nickraymond/nereus_Pi_shield_ADIN2111/docs/design-review/qe/S7.md

# QE reviews — S7 (PR #29 S7.a)

*Reports from the standing S7 Quality Engineer session (started 2026-10-07 from a task chip, Opus 5.5 high, read-only),
sent straight to the design session and saved by the design agent. Newest round first. Design-agent responses follow
each round.*

---

## PR #29 (S7.a) — Round 3 — 2026-10-07 — APPROVED

**Reviewed:** cce774f (b8083da + cce774f vs 2339368; base b365929), from a `git archive` copy; no fetch.

| Claim | Result | Evidence (summary) |
|---|---|---|
| R2-N1 Bus row names only the T1/T2 data legs and D4/D5 TVS legs | PASS | matches pcbnew |
| R2-N2 | PASS (moot) | the notch was then removed |
| Nick: plain 46 × 65 rectangle, r 3, no notch; §11 notch bullets gone | PASS | no notch coordinates left anywhere; also clears round 1's H2 keep-out point |
| Nick: QE agent file carries the D31 exception | PASS | wording matches CLAUDE.md, SPEC c1, TRACKER 8/9; round-1 N5 closed |
| Round-2 report recorded faithfully; TRACKER, checklist (script parses) | PASS | |
| No schematic / board / reference / Archive / tools change; checks unchanged | PASS | ERC 0 / 494, ercexclude 18/0/0/0, midwire 0, netcheck 51/51 |

| # | Severity | Finding |
|---|---|---|
| R3-N1 | NIT | TRACKER and checklist don't record round 3 |
| R3-N2 | NIT | round-2 response mentions the notch spans that cce774f superseded |

Repo untouched (clean before/after).

### Design-agent response
R3-N1: TRACKER and checklist record round 3. R3-N2: round-2 response annotated.

---

## PR #29 (S7.a) — Round 2 — 2026-10-07 — APPROVED WITH NITS

**Reviewed:** 2339368 (diff vs e735ed6; base b365929), from a `git archive` copy; no fetch this round.

| Claim | Result | Evidence (summary) |
|---|---|---|
| F1 pullback 3.85–4.78 mm in SPEC, BRIEF §4, PR body | PASS | matches the round-1 point-to-segment measurement |
| F2 §6 classes for new routing only; §8.4 / §8.5 consistent | PASS | every mote bus track under 1.0 mm ends at D4/D5 or T1/T2 pins 6/7, so the carve-outs cover them |
| F3 notch transform, shape, edge exemption, §11 | PASS | maps Nick's x 193.78–225.28 to −0.75…30.75; ≈ 2.76 mm from H2 |
| F4 renderer net names | PASS | shield-style names map to bus / pin / pi5v / rail / data / 3v3; switch nets stay signal; mote re-render OK |
| F5 D31 wording, D6 stands | PASS | DESIGN D31, BRIEF §11 |
| N1–N4; N5 left for Nick | PASS / accepted | |
| Round-1 report saved faithfully; TRACKER, checklist (script parses) | PASS | |
| No schematic / board change; checks unchanged | PASS | ERC 0 / 494, ercexclude 18/0/0/0, midwire 0, netcheck 51/51 |

| # | Severity | Finding |
|---|---|---|
| R2-N1 | NIT | §6 mentions "0.2 mm test-point taps" on the bus nets; the mote has none (narrow bus copper ends at T1/T2 pins 6/7 or D4/D5) |
| R2-N2 | NIT | §2's notch span x 5.84…25.66 is where the chamfers start; at the edge it is 4.42–27.08, at full depth 7.58–23.91 |

Repo untouched (clean before/after).

### Design-agent response
R2-N1: the Bus row now names only the data legs to T1/T2 (0.2 mm) and the TVS legs to D4/D5 (0.5 mm). R2-N2: §2 quotes
the edge and full-depth spans (notch later removed by Nick, cce774f). (Round 1's response above mentions "test-point taps"; left as recorded.)

---

## PR #29 (S7.a) — Round 1 — 2026-10-07 — CHANGES REQUESTED

**Reviewed:** e735ed6 vs b365929, from `git archive` copies; BRIEF, KICKOFF, render_layers.py, CLAUDE.md, SPEC, TRACKER,
DESIGN D31, SOFAR_QUESTIONS, DEV_LOG, checklist. Mote board read with pcbnew (never saved); Pi drawing RP-008358-DS-1 and
the Bourns SRF1260 datasheet fetched.

| Claim | Result | Evidence (summary) |
|---|---|---|
| No schematic / board / reference / Archive change; check.sh unchanged | PASS | ERC 0 / 494, ercexclude 18/0/0/0, midwire 0, netcheck 51/51 |
| Pi Zero 2 W holes, header, pin 1 (25.23, 8.37), pins 39/40 y 56.63, orientation | PASS | Drawing: 65 × 30, holes 3.5 in, header centre 3.5 + 29; 90° CW rotation, not a mirror |
| J1 on B.Cu puts pin 2 east of pin 1; courtyard clears H2/H4 | PASS | by 0.07 / 0.13 mm |
| Insert arc, 7 vias at r 3.0, ring pad r 2.2–3.69, body Ø6 × 1.5 | PASS | pcbnew; D24 |
| Planes 4.1–4.8 mm from inserts | **FAIL** | 3.85 mm at MP2/MP4 (F1) |
| Insert placement, pocket, squeeze band, U1 courtyard, Micro-Fit courtyard, J5 vs L1 (0.09 mm), L2, M3 vs inserts | PASS | geometry checked |
| Block ref lists vs schematic | PASS | every ref in exactly one row; TP38 not on the mote (N1) |
| ADIN pair lengths, vias through-only | PASS | 9.47 / 8.01 / 18.25 / 21.30 mm |
| Sofar Q9–Q12 claims | PASS | datasheet windings 1–3, 2–4; nets and fitted state; slots, islands, stackup |
| render_layers.py → six SVGs | PASS (mote) | shield names fail the colour map (F4) |
| Scoped exception wording; SPEC via fact; TRACKER / checklist / DEV_LOG | PASS | plane distance aside (F1) |
| Area-check percentages | not verified | labelled an estimate |

| # | Severity | Finding |
|---|---|---|
| F1 | MINOR | Plane pullback is 3.85 mm (MP2/MP4) to 4.78 mm (MP1/MP3), not 4.1–4.8 (SPEC, BRIEF §4, PR body) |
| F2 | MAJOR | §6 bus ≥ 1.0 mm and VBUS/P_IN ≥ 0.5 mm contradict the copper §5/§8.4 say to copy exactly (0.2 mm bus legs to T1/T2 and taps, 0.5 mm to D4/D5, 0.2 mm sense legs), so §8.4 and §8.5 can't both pass |
| F3 | MINOR | The SD notch's east end is inside H2's r 3.0 keep-out (≈ 2.76 mm on Nick's shape); its x values rest on an unstated mapping, and the brief describes a rectangle where Nick drew a fillet–chamfer–fillet notch |
| F4 | MINOR | render_layers.py matches bare net names; the shield's nets are hierarchical, so its renders lose the bus / P_IN / Pi 5 V / AVDD colours |
| F5 | MINOR | D6 (plain socket, no stacking header) contradicts D31 ("also the target for the real layout") |
| N1 | NIT | TP38 is new (5V_PI), filed under "as on the mote" |
| N2 | NIT | "Mote parts not on the shield" omits U9, D6, D7, R9, R10 |
| N3 | NIT | ADIN pairs are on L1 + L2 on the mote, not "on L2" |
| N4 | NIT | Hole_M3 courtyard / silk run past the outline at MTG1–4; Ø6 pad at exactly 0.5 mm from the edges |
| N5 | NIT | `.claude/agents/quality-engineer.md` still checks "no .kicad_pcb modified" without the D31 exception |
| N6 | NIT (QE process) | QE ran one `git fetch origin` (remote-tracking refs only) |

Repo untouched (clean before/after).

### Design-agent response
F1: re-measured with point-to-segment distances (my first pass used polygon vertices only): 3.85 mm at MP2/MP4, 4.78 mm
at MP1/MP3. SPEC and BRIEF §4 corrected; the brief keeps r 4.8 as its own choice; PR body updated. F2: §6 now sets
classes for **new routing** only (bus DC path insert ↔ inductor ≥ 1.0 mm; rail copper ≥ 0.5 mm); copied copper keeps
Sofar's widths (0.2 mm data legs, taps and sense legs, 0.5 mm TVS legs) and is judged by §8.4; §8.5 checks new routing
only. F3: §2 copies the notch from User.3 translated by (−194.53, −58.48) (Nick's 31.5 mm outline centred on the Pi),
describes its shape, makes the board edge exempt from H2's keep-out and lists the clearance for Nick in §11. F4:
`group()` strips the hierarchical prefix; `3V3` and the Pi 5 V nets are exact matches (switch / feedback nets stay
"signal"); re-run on the mote → six SVGs; shield-style names now map to bus / pin / pi5v / rail / 3v3. F5: D31 now says
"proposed as the target" and the stacking header is the experiment's assumption, D6 standing until Nick picks J1; §11 says
the same. N1: TP38 moved to BUCK5V. N2: "anything not in our netlist" with the full example list. N3: "layers as the
mote (L1 + L2, two vias each)". N4: the brief tells the agent to clip silk and record the courtyard-edge items with the
reason. N5: left for Nick (an edit to the QE's own agent definition). N6: noted.
