nickraymond/nereus_Pi_shield_ADIN2111/docs/design-review/qe/S6.md

# QE reviews — S6 (PR #22 S6.a, PR #23 S6.b, PR #24 S6.c, PR #25 S6.d, PR #26 S6.e, PR #27 S6.f, PR #28 S6.g)

*Reports from the standing S6 Quality Engineer session (started 2026-10-06 from a task chip, Opus 5.5 high, read-only),
sent straight to the design session and saved by the design agent. Newest round first. Design-agent responses follow
each round.*

---

## PR #28 (S6.g) — Round 3 — 2026-10-07 — APPROVED

**Reviewed:** ece1959 vs 62d0605. The only schematic change is the ~{PAYLOAD_FAULT} stub on Top-Level (jogged 2.54 mm
down, as declared); the other changes are the changelog, DEV_LOG, this log and schematic.pdf. Netlist identical to round 2
(names and pins); ERC 0 / 494 with the same items; ercexclude 18/0/0/0, midwire 0, netcheck 51/51; in the render the
overbar sits a full grid step below the PAYLOAD_EN wire. No findings.

### Design-agent response
Merged on Nick's OK ("merge it once the QE approves").

---

## PR #28 (S6.g) — Round 2 — 2026-10-07 — APPROVED WITH NITS

**Reviewed:** 62d0605 (round-1 nits + Nick's follow-ups: J5 beside the Load Switch, R11 note, J1 / Load Switch headers,
Power title removed).

| Claim | Result | Evidence |
|---|---|---|
| Connectivity | PASS | netlist identical to round 1 incl. names; J5.1 VBUS_OUT, J5.2 GND |
| ERC / checks | PASS | 0 / 494 (+2 off-grid for the pin-48 jog; U1 pin 48 off-grid in Sofar's symbol); ercexclude 18/0/0/0, midwire 0, netcheck 51/51 |
| Scope | PASS | uuid-for-uuid diff: exactly the declared changes |
| Visual | PASS | ~{ADIN_P2_LED1} clear of R4; 1V8 header clear of its wire; J5 + note beside the Load Switch; R11 note right for open and fitted; new headers match the style |

| # | Severity | Finding |
|---|---|---|
| N1 | NIT (optional) | Top-Level: ~{PAYLOAD_FAULT}'s overbar lies on the PAYLOAD_EN wire 2.54 mm above it (missed in round 1) |

### Design-agent response
N1: same fix as ~{ADIN_P2_LED1}: the label sits 2.54 mm lower on a jogged stub, clear of the PAYLOAD_EN wire. Pin
partition unchanged (109 nets); ERC 0 / 494 unchanged (all on grid); ercexclude 18/0/0/0, netcheck 51/51, midwire 0;
rendered and checked.

---

## PR #28 (S6.g) — Round 1 — 2026-10-07 — APPROVED WITH NITS

**Reviewed:** 25d8f57 vs 1cc371c, from git archive; all 7 sheets rendered and looked at.

| Claim | Result | Evidence |
|---|---|---|
| 1. Pin partition; 7 renames | PASS | 134 comps same value+footprint; 109 nets identical pin sets; exactly the 7 declared renames; polarity right (PAYLOAD_EN → U11 ~SHDN high = on; FLT, INT, RESET, CS, LED_1 active low) |
| 2. ERC / exclusions / checks | PASS | 495 → 492 (off-grid 481 → 479, multiple names 12 → 11); −2 off-grid, −1 SW_ON/SW_EN; 8 keys changed, same uuids/types/paths, 18 reasons identical; ercexclude 18/0/0/0, midwire 0, netcheck 51/51, 8 test suites OK |
| 3. Items / visual | PASS | Top-Level, ADIN, Power, cover and title blocks as declared; no leftover ${…} overlays; nothing straddling |
| 4. Hard rules | PASS | no .kicad_pcb / library / reference / Archive diff |
| 5. Docs / PDF | PASS | D30, pin map, results row, changelog, README, sofar_brief, TRACKER, viewer, DEV_LOG; schematic.pdf = QE export |

| # | Severity | Finding |
|---|---|---|
| N1 | NIT | ~{ADIN_P2_LED1}'s new overbar lands on pin 47's wire to R4 just above |
| N2 | NIT | the 1V8 header starts on the vertical 3V3 → 1V8 feed wire |
| N3 | NOTE (Nick) | the cover keeps Sofar's CC BY-ND 4.0 notice on a board "Derived from" their mote; BY-ND generally doesn't allow sharing adapted material; nothing in docs/ discusses it |

### Design-agent response
N1: pin 48's stub jogs down 2.54 mm and the label sits on it, clear of pin 47's wire (pin partition unchanged). N2: header
2.54 mm right. N3: SOFAR_QUESTIONS Q8 drafted for Nick to send (how the shield may be shared; what licence text the
cover should carry).

---

## PR #27 (S6.f) — Round 1 — 2026-10-07 — APPROVED WITH NITS

**Reviewed:** dac10bb vs d994716, from git archive.

| Claim | Result | Evidence |
|---|---|---|
| 1. Only AUTHOR changes; all 7 sheets render it | PASS | one .kicad_pro line; netlist only the textvar line; 7/7 SVGs "Nick Buemond", 0 "ProjectAuthor" |
| 2. bom.pdf from bom.csv; 51 / 105 + 1 DNP / 11 highlighted | PASS | counts from bom.csv match the header; rebuild reproducible (only trailer metadata differs); page 1 rows equal bom.csv cell for cell |
| 3. schematic.pdf | PASS | 17/17 content streams identical to the QE's export |
| 4. Docs | PASS | consistent |
| 5. Checks / hard rules | PASS | 495/0/495; 18/0/0/0; midwire 0; 51/51; no sheet/pcb/reference/Archive/library change |

| # | Severity | Finding |
|---|---|---|
| N1 | NIT | bom.pdf is a snapshot outside check.sh (silently stale if bom.csv changes; header date is the build day) |
| N2 | NIT | bompdf.py has no test |

### Design-agent response
N1: README says both PDFs are snapshots not rebuilt by check.sh, to rebuild after schematic/BOM changes, header = build
date. N2: `tools/test_bompdf.py` (counts, highlight, escaping). Also (Nick hit it): the README's commands now say they run
from the repository root, with a `cd` example. Merged.

---

## PR #26 (S6.e) — Round 1 — 2026-10-06 — APPROVED WITH NITS

**Reviewed:** d5a16bd vs afab634, from git archive.

| Claim | Result | Evidence |
|---|---|---|
| 1a. README files exist, numbers match | PASS | all named files/sections present; ercsum 481/12/2, 0/495; bom.csv 51 lines; footprints.md 43 rows |
| 1b. Open questions match SOFAR_QUESTIONS / SPEC | PARTIAL (F1) | Sofar Q2/Q6/Q7 open, Q1/Q4/Q5 deferred, Q3 answered: correct; 4 open SPEC items missing |
| 1c. footprints.md "Used by" | PASS | all 43 rows = the shield netlist's Vault users |
| 2. schematic.pdf | PASS | same size and 17/17 decompressed content streams as the QE's export; only CreationDate differs |
| 3. new_nets | PASS (N1) | reproduces; every row = its net's full pin set; J1.1 + J1.17 on their own net (constraint 4 holds) |
| 4. Jumper Descriptions | PASS (N2) | exactly 5 Description lines; netlist only those values |
| 5. Checks | PASS | 495/0/495; 18/0/0/0; midwire 0; 51/51; 7 test suites OK; no .kicad_pcb/.kicad_pro/library/reference/Archive change |
| 6. Docs | PASS | consistent |

| # | Severity | Finding |
|---|---|---|
| F1 | MINOR | README omits 4 open SPEC items: ADIN2111 power allowance (S6), Murata undersea warranty note (S6), U10/L6/L1 heat (bring-up), Pi data-port USB VBUS (D14) |
| N1 | NIT | netcheck section says "not on the mote board" but includes MP1–MP4 (on the board, unnumbered insert pads) |
| N2 | NIT | Description fix has no source in the changelog and no sofar_brief line |
| N3 | NIT | power_budget.md payload conclusion still reasons with U9 / 0.74 A |

### Design-agent response
F1: 2 bullets under "For the design review" and a new "For Nick (bring-up)" list with the other 2, each with SPEC's
citation. N1: section wording names MP1–MP4 (netcheck.md regenerated). N2: changelog cites the MPN code, the S5.e row
and the RESISTANCE field; sofar_brief import-housekeeping line. N3: one-line U11 note in the conclusion. Merged.

---

## PR #25 (S6.d) — Round 1 — 2026-10-06 — APPROVED WITH NITS

**Reviewed:** 4174bfb vs 8765cf7, from git archive; rendered base vs head (kicad-cli svg → qlmanage).

| Claim | Result | Evidence |
|---|---|---|
| 1. Connectivity unchanged | PASS | 134 comps identical value+footprint; 109 nets identical names and pin sets |
| 2. ERC 504 → 495; checks | PASS | −9 `unconnected_wire_endpoint` (6× 40.64, 2× 20.32, 1× 22.86 mm wires), nothing added; one .kicad_pro key (#PWR34 y), same uuid; ercexclude 18/0/0/0; 51/51; midwire 0 |
| 3. Top-Level items | PASS | item-level diff by uuid matches every declared move/removal; nothing else; J1 not moved |
| 4. ADIN items | PASS | R46/D10, R3/R5, #PWR49/#PWR34, labels, R4/R6 fields, note box exactly as declared; nothing else |
| 5. Declared not done | PASS | J1 position; 2 PoDL dangling ends |
| Visual review | PASS | I²C pull-ups inline on J1's stubs; LEDs at an even pitch; text off wires/junctions; notes no longer wrap; nothing beyond minor |
| Hard rules | PASS | no .kicad_pcb / reference / Archive / library change |

| # | Severity | Finding |
|---|---|---|
| N1 | NIT | #PWR77/#PWR78 at 2.54 mm draw as one continuous bar with two "3V3" texts (optional) |
| N2 | NIT | junction at (292.1, 119.38) now joins only TP8's pin and one wire: redundant |
| N3 | NIT | ADIN_VDDIO symbols under R3/R5 point down (unambiguous; optional) |
| N4 | NIT | TRACKER "as he drew them": Sofar is a company |
| N5 | NIT (pre-existing) | MP1–MP4 reference text overlaps their bodies; TP5/TP7 labels crowd |

### Design-agent response
N2: junction removed (nets identical, midwire 0, ERC 495/0/495). N4: "as Sofar drew them". N1, N3, N5 left as the QE
allows and listed for Nick in the package README. Merged.

---

## PR #24 (S6.c) — Round 1 — 2026-10-06 — APPROVED WITH NITS

*(Queued; read from the QE's transcript.)* **Reviewed:** 9fa17eb vs ab5efd6.

All 43 files insertions only (41 lines each: one type line, four 0.05 mm F.CrtYd lines; no pad line changed);
`fpextract --verify` 0 problems; types match KiCad's stock footprints; every courtyard read back with KiCad Python is a
closed rectangle enclosing all pads with ≥ 0.1 mm clearance, sizes and 8/31/4 sources as documented; second run all
"kept"; no schematic / project / check.sh change (504/0/504, 51/51); no .kicad_pcb / reference / Archive / nereus.pretty
change; tests pass.

| # | Severity | Finding | Fix |
|---|---|---|---|
| F1 | MINOR | `footprints.md` "Used by" column wrong on 5 rows (e.g. J1 on the insert footprint, U11 on an 0805) | generate from the shield netlist; no re-review needed |
| — | note | AP22913 (U2/U3) courtyard is tight (0.05 mm past the body) — Sofar's own outline | for Nick's layout |
| — | note | Update Footprints from Library replaces the board footprints; its options decide whether text/field positions are kept | for Nick's layout |

### Design-agent response
F1: my regex ran across component boundaries in the netlist; the column is now parsed per component from the shield's
netlist (6 rows corrected, incl. the unused R10 spare marked "unused") and its header says so. Both notes added to the
TRACKER item for Nick's layout. Merged.

---

## PR #23 (S6.b) — Round 2 — 2026-10-06 — APPROVED WITH NITS

*(Queued again; read from the QE's transcript.)* **Reviewed:** 13a40bf vs 3bb0e42.

F1 fixed (8 unjustified → exit 1; clean → 18/0/0/0, exit 0); F2 MTG reason in the table and the 4 comments, keys
unchanged; N1 two-item errors reported, 5 tests pass; diff limited to the 6 listed files; ERC 504/0/504, netlist,
netcheck 51/51, midwire 0 unchanged.

| # | Severity | Finding |
|---|---|---|
| N1 | NIT | a hand exclusion (as the tool advises for two-item errors) would still fail the check, and `--write` would delete it |
| N2 | NIT | check.sh's exit-code comment doesn't mention unjustified errors |
| — | note | S6.d moves symbols: regenerate keys with `--write`; QE will check only keys change, not the 18 reasons |

### Design-agent response
N1: exclusions whose comment starts with "manual:" are kept by `--write` and stay applied when the tool runs ERC; new
test (6/6). N2: comment updated. Merged.

---

## PR #23 (S6.b) — Round 1 — 2026-10-06 — CHANGES REQUESTED

*(Report queued by the QE but not delivered; read from its transcript.)*

**Reviewed:** 3bb0e42 vs 0fdc10b.

Verified: ERC 531/27/504 → 504/0/504, warnings identical; 9 title-block errors fixed (rev AA, PCB-000001-AA, name); 18
exclusions each point at the right symbol/pin; every reason holds against the files (FID/MTG no net on the mote board;
switch/bootstrap pins; inductor- or passive-VOUT-fed rails); only the 7 revs + 3 text variables change in the netlist;
no .kicad_pcb / reference / Archive change; title blocks render "Rev: AA" and PCB-000001-AA ("=ProjectAuthor" declared).

| # | Severity | Finding | Fix |
|---|---|---|---|
| F1 | BLOCKING | `tools/ercexclude.py` exits 0 with unjustified errors (deleted a title-block variable on a copy: "8 unjustified", exit 0), so check.sh wouldn't gate new errors (e.g. from S6.d) | also return 1 on unjustified |
| F2 | MINOR | MTG1–4 were listed as Nick's board decision (grounding); the new reason only says "kept as Sofar has it" | say grounding stays Nick's decision |
| N1 | NIT | tool assumes single-item errors; a two-item error would show as stale on every run | handle explicitly |

### Design-agent response
F1: `main` returns 1 on unjustified, stale or missing; reproduced the QE's case (PCBPARTNUMBER removed → "8 unjustified",
check.sh exit 1; restored → exit 0). F2: MTG reason now ends "grounding the holes stays Nick's board decision" (the 4
exclusion comments regenerated). N1: two-item errors are reported as "exclude in KiCad by hand" (unjustified) instead of
keyed; new test. Tool tests 5/5.

---

## PR #22 (S6.a) — Round 1 — 2026-10-06 — APPROVED WITH NITS

**Reviewed:** bb20672 vs base f26e414, from `git archive`; 6 sheet files, bom.csv, docs, viewer.

| Claim | Result | Evidence |
|---|---|---|
| 1. 26 `in_bom yes→no` on TP/FID/MTG; nothing else in those blocks | PASS | per-block parse: exactly those 26 refs, `in_bom` only; all TP bare copper, FID fiducial, MTG Hole_M3; only other `in_bom no` = JP1/JP2 |
| 2. MANUFACTURER on 75 parts (76 blocks) from bom_lifecycle; J1 skipped; existing untouched; D1 = STMicroelectronics | PASS | 76 hidden properties, each = lifecycle Mfr for its MPN (R11 via its Value row); 30 existing byte-identical; Sofar's MFR_NAME / MANUFACTURER1 / "MANUFACTURER 1" unchanged |
| 3. No other change; root untouched | PASS | file text outside symbol blocks identical; deletions = 26 `(in_bom yes)` lines |
| 4. Netlist | PASS | 109 nets identical pin sets; 134 comps identical value+footprint; +26 exclude_from_bom, rest MANUFACTURER |
| 5. ERC | PASS | 531/27/504 both; only the flapping multiple_net_names item differs (reproduced flapping on base) |
| netcheck / midwire / tests | PASS | 51/51, 0, all OK |
| 6. bom.csv | PASS | preset export cmp-identical; 51 rows; Mfr blank only on J1 |
| 7. Docs | PASS | TRACKER, viewer, bom_lifecycle, changelog, DESIGN, DEV_LOG agree |
| Hard rules | PASS | no .kicad_pcb / reference / Archive change |

| # | Severity | Finding | Suggested fix |
|---|---|---|---|
| N1 | NIT (optional) | Mfr spellings differ between rows: Sofar's values ("Yageo / Phycomp", "Wurth Elektronik", "Bourns Inc.", "Hubei KENTO Elec", "Kemet", "Vishay") beside the lifecycle names ("Yageo", "Würth Elektronik", "Bourns", "Vishay Dale") | leave Sofar's data; one sentence in S6.e's package |

Repo untouched (clean before/after).

### Design-agent response
N1: noted as an S6.e package item (TRACKER); Sofar's fields stay as they are. Merged.
