nickraymond/nereus_Pi_shield_ADIN2111/docs/design-review/qe/S5.md

# QE reviews — S5 (PR #11 S5.a, S5.b, PR #14 S5.c, PR #15 S5.d, PR #16 S5.g, PR #17 S5.f, PR #18 S5.e, PR #20 S5.h, PR #21 S5.i)

*Reports from the standing S5 Quality Engineer session, sent straight to the design
session and saved by the design agent. Newest round first. Design-agent responses
follow each round.*

---

## PR #21 (S5.i) — Round 1 — 2026-10-06 — APPROVED WITH NITS

**Reviewed:** 9e6bcf4 vs base 1acef25, from git archives; worktree read only.

| Claim | Result | Evidence |
|---|---|---|
| 1. PLANNED ×4 on 106 parts / 107 blocks, 428 fields | PASS | each block gains exactly the 4 fields, hidden, appended; none on TP/FID/MTG/JP1/JP2 |
| 2. Ten changed lines = plan; D1; J1 | PASS | all values match bom_alternates.md "Planned parts"; D1 Vishay, LCSC empty; J1 TBD |
| 3. Every other part = Value + lifecycle Mfr/LCSC | PASS | 66 "in LCSC stock" notes all on lifecycle-OK parts; 11 "no LCSC listing" = D2, D3, L3, L6, MP1–4, U1 ×2, Y1; specials match lifecycle facts |
| 4. R8 reasoning | PASS (arithmetic) | pad inner edge 0.10 mm from centre; PMR03 runs 0.35 mm under the body, UR73 0.15 mm. Datasheet b values not re-read (no PDFs) |
| 5. SOURCING on 19; 5 re-indents; nothing else | PASS | 24 removed sheet lines = 19 old SOURCING + 5 Footprint (4 tabs), re-added at 2 tabs identical |
| 6. Netlist / ERC / netcheck / midwire | PASS | 38 removed netlist lines, all SOURCING; nets/values/footprints identical; ERC 27/504 items identical; 51/51; 0 |
| 7. .kicad_pro preset + check.sh + bom.csv | PASS | preset/bom_settings as declared; unknown preset exits 2; exports byte-identical to bom.csv, 54 rows, 11 Planned ≠ Value |
| 8. Docs | PASS (N2) | D27, bom_alternates, bom_lifecycle, sofar_brief, changelog, TRACKER, viewer (compiles), DEV_LOG |

| # | Severity | Finding | Suggested fix |
|---|---|---|---|
| F1 | MINOR | Two Planned notes contradict the plan's stock figures: R21 group "largest LCSC stock" (ALT2 YAGEO C60491 has 8.4 M vs 2.4 M); C16 group "the AVX ALT2 has too few for 80" (750 ≥ 80) | "ample LCSC stock"; "250,730 vs the AVX ALT2's 750" |
| N1 | NIT | C17/C26 "TDK's other catalog number for the same …" not backed by a source; K125AB fixes 1.25 mm thickness, KT000N doesn't state it | "TDK C2012 series, same spec (thickness not confirmed)" |
| N2 | NIT | D26 unchanged though D27 amends it | append "(amended by D27)" |
| N3 | NIT (optional) | C21 "tier-1 maker" is judgement presented as the why | reword |

Could not verify: the two datasheets' b values (no PDFs). Repo untouched (clean before/after, 9e6bcf4).

### Design-agent response
F1: R21 group note → "ample LCSC stock"; C16 group → "largest LCSC stock (250,730 vs the AVX ALT2's 750, 2026-10-06)".
N1: C17/C26 → "TDK C2012 series, same 1 µF ±10 % 100 V X7S 0805 per LCSC (thickness not confirmed: K125AB is 1.25 mm,
KT000N doesn't state it)"; bom_alternates and DEV_LOG to match. N2: D26 now says "(amended by D27 …)". N3: C21 → "from
Taiyo Yuden, an established MLCC maker". Datasheet URLs for R8 added to bom_alternates.md. Only these 11 PLANNED NOTE
lines changed in the sheets; ERC 531/27/504, netcheck 51/51. Merged on Nick's instruction ("if the QE approves, merge").

---

## PR #20 (S5.h) — Round 3 (Symbol Fields Table preset) — 2026-10-06 — APPROVED

**Reviewed:** 295f0e0 vs 50ca8c1, from git archives; worktree read only.

| Claim | Result | Evidence |
|---|---|---|
| Only the .kicad_pro changed in the project | PASS | `git diff --quiet` on the project (excluding .kicad_pro) and tools/: no change; bom.csv unchanged |
| Only the BOM view keys changed | PASS | Deep JSON compare: only /schematic/bom_presets (new) and bom_settings name / fields_ordered / include_excluded_from_bom |
| Preset content | PASS | One preset "Sofar review (alternates)", columns and labels as declared, grouped by Value + DNP, BOM-excluded hidden, sort Reference asc; bom_settings equals it, so the dialog opens on it |
| Formatting | PASS | indent-2 / ensure_ascii=False round-trips old and new files byte-identically |
| Preset export = bom.csv | PASS | `kicad-cli sch export bom --preset …`: 54 rows, same 54 groups, 0 differing cells |
| check.sh state unchanged | PASS | ERC 27/504 (items identical with locations stripped); netlist identical to round 2; netcheck 51/51; midwire 0 |
| Docs / viewer | PASS | changelog, TRACKER, viewer (script compiles), DEV_LOG |

No findings. Note: KiCad rewrites the .kicad_pro on close (bom_settings filled with every imported field); discard that after Nick's
look rather than commit it. Repo untouched (clean before/after, 295f0e0).

---

## PR #20 (S5.h) — Round 2 — 2026-10-06 — APPROVED

**Reviewed:** cdfee7e vs d2cdfab (commits f5415f2, cdfee7e), from git archives; worktree read only.

| Claim | Result | Evidence |
|---|---|---|
| Only R8 ALT NOTE and J1 SOURCING changed in the project | PASS | Patience diff of the project + tools/: exactly two property lines; R8 note exact; J1 "2x20" → "2×20" (plan text) |
| Netlist vs d2cdfab | PASS | Only those two values (component property + libpart field each); nets, values, footprints unchanged |
| R8's Sofar alternates | PASS | MANUFACTURERPARTNUMBER1–7 unchanged; none (nor the field names) in bom.csv |
| ERC / netcheck / midwire | PASS | 27/504, ercsum items identical with locations stripped; 51/51; midwire 0 |
| bom.csv | PASS | check.sh's export byte-identical to the tracked file, 54 rows; vs d2cdfab only the J1 and R8 rows differ |
| C22/C23 DK-figure drop declared | PASS | changelog note |
| Cap of 3 alternates | PASS | D26 and bom_alternates.md; ours ≤ 2; Sofar's own listed alternates stay in their fields, outside bom.csv |
| Docs / viewer | PASS | qe/S5.md, TRACKER, viewer (script parses under JavaScriptCore), DEV_LOG |

No findings. Repo untouched (clean before/after, cdfee7e).

---

## PR #20 (S5.h) — Round 1 — 2026-10-06 — APPROVED WITH NITS

**Reviewed:** d2cdfab (PR head) vs base 1e9a1c7, from git archives; worktree read only.

| Claim | Result | Evidence |
|---|---|---|
| 1. 24 passives × 8 hidden fields, values = plan | PASS (N1) | Every symbol's properties parsed base vs head: 24 refs gain exactly the 8 fields; ALT1/ALT2 MPN/MFR/LCSC match bom_alternates.md; empty exactly for R20/R39 ALT2, R15/R16 ALT2, C22/C23 both; SOURCING text on all 24; ALT NOTE = plan text without `**`, plus "ALT1 is JLC Basic" (R21 group) and "ALT2 AEC-Q200" (R14/R18), both backed by the plan's stock columns |
| 2. SOURCING-only parts, 208 total | PASS (N1) | 16 blocks: U1 ×2, U2, U3, L3, L6, Y1, D1–D3, MP1–MP4, J5, J1; values = plan except J1 (N1); 24 × 8 + 16 = 208 |
| 3. Existing properties unchanged, nothing outside symbols, all hidden | PASS | All 7 sheets item by item: existing properties byte-identical and in order, new ones appended with `(hide yes)`; one removed line in a patience diff, J1's Footprint (4 → 2 tabs, same text); root sheet unchanged; no raw newlines in quoted strings |
| 4. Netlist vs main | PASS | Base/head exports: apart from 4 path-dependent header lines, 0 removed, 414 added, all ALT/SOURCING lines; nets (109), pins, values, footprints, DNP identical |
| 5. ERC / netcheck / midwire / bom.csv | PASS | ERC 27/504 both sides, ercsum item lists identical with locations stripped; netcheck 51/51 (report = committed netcheck.md); midwire 0; tool tests OK; BOM export twice, byte-identical to each other and to the tracked bom.csv (54 rows) |
| 6. `${DNP}` column + group by Value, DNP | PASS | R11 its own DNP row; R12/R13/R17/R19 fitted (Qty 4); Value (MPN) the primary column with Sourcing and alternates beside it, as Nick asked |
| 7. Docs | PASS (N3) | bom_alternates, bom_lifecycle, sofar_brief, changelog, DESIGN, TRACKER, DEV_LOG agree with the files |

| # | Severity | Finding | Suggested fix |
|---|---|---|---|
| N1 | NIT | Three undeclared text differences from the plan: R8 ALT NOTE en dash → hyphen ("1–7"); C22/C23 ALT NOTE drop "(DK 78,606)"; J1 SOURCING "2×20" → "2x20" | Declare in the changelog or match the plan |
| N2 | NIT | bom.csv also lists 16 TPs, FID1–6, MTG1–4 (26 placements, `in_bom yes` since the import): Qty total 132 = 105 + R11 + 26. A JLC order would need them dropped | Note for S6 (`in_bom no` or filter the export) |
| N3 | NIT | Viewer item already titled "S5.h: QE approved; your KiCad look" while TRACKER's QE item is open | Fine once this approval is recorded |

Repo untouched (clean before/after, d2cdfab).

### Design-agent response
N1: J1 SOURCING back to "2×20" (plan text). R8 ALT NOTE replaced at Nick's decision (alternates capped at 3; ours are ≤ 2; R8's 7 Sofar
fields stay untouched and out of bom.csv): now "Sofar review: power-path current sense; check land pattern". C22/C23 drop of the DK
figure is deliberate (stock drifts; the figure stays in bom_alternates.md) — declared in the changelog. N2: added to TRACKER S6 (BOM
export for JLC). N3: TRACKER and viewer QE items ticked.

---

## PR #18 (S5.e) — Round 2 — 2026-10-06 — APPROVED WITH NITS

**Reviewed:** 715e523 vs 98d53a2, docs only.

| Claim | Result | Evidence |
|---|---|---|
| F1 constraints 7/8 note | PASS | Sofar parts stay; exact-part routes keep both constraints; substitution needs an amendment; exceptions listed |
| D26 sourcing policy | PASS | consistent across the doc, TRACKER, viewer |
| † rows | PASS | D2/D3, R8, R15/R16, commodity R/C (R34 ours) |
| N1–N4 | PASS | Y1, MP, R15/R16 TCR, U2/U3 |
| TRACKER / viewer | PASS | |

| # | Severity | Finding | Suggested fix |
|---|---|---|---|
| F1 | MINOR | The policy doesn't say how the flagged passives are bought for this 20-board build (no LCSC stock): until Sofar approves an alternate they too must go through JLC global sourcing or consignment | One line in D26 and the doc |
| N1 | NIT | Tick TRACKER "S5.e: QE review" with the round-2 result | — |

Repo untouched (clean before/after, 715e523).

### Design-agent response
F1: D26 and bom_lifecycle.md say every flagged passive is bought exact via JLC global sourcing (or consigned) for the first build until an alternate is approved. N1: TRACKER ticked.

---

## PR #18 (S5.e) — Round 1 — 2026-10-06 — CHANGES REQUESTED

*(Read from the QE transcript: the message tool had paused the QE's sends.)* **Reviewed:** 98d53a2 vs e62d974, docs only.

| Claim | Result | Evidence |
|---|---|---|
| BOM scope matches the netlist | PASS | 50 unique / 105 placements after exclusions; all rows match netlist refs |
| Summary counts | PASS | 29 / 12 / 6 / 1 / 1 / 1 |
| D1 obsolete; second sources | PASS (partly unverified) | fields name Vishay SMA6F33A-M3/H and ST SMA6F33AY; R8's 7 alternates present; Digi-Key not loadable, other distributors show ST discontinued |
| U1, MP1–4, L3/L6, Y1 absent at LCSC | PASS (as caveated) | restricted searches found none |
| U2/U3 at 30; C22/C23 out of stock | PASS | confirmed; potting remark correct |
| J1 | PASS | 95157-440LF is an SMD male header; both candidates female TH 2×20, 8.5 mm |
| 10 sampled OK rows | PASS | MPN matches C-number; stock ≥ 20 boards |
| Equivalents (sampled) | PASS (nits) | value-for-value except R15/R16 (N3) |
| Docs consistency | PASS | |

| # | Severity | Finding | Suggested fix |
|---|---|---|---|
| F1 | MAJOR | The doc offers "an LCSC equivalent" for Sofar parts and suggests swaps (D2/D3, R8, R15/R16, commodity R/C) without saying SPEC constraints 7 and 8 forbid them | Constraints note; exact-part buying keeps both; substitutes need a constraint 8 (and 7) amendment except Sofar's listed alternates and our own parts; mark affected rows |
| N1 | NIT | LCSC same-family Y1 crystals aren't drop-ins (−20…+70 °C; 8 pF) | One line in the Y1 row |
| N2 | NIT | JLC lists taller Würth M3 inserts (3.0 / 4.0 mm) | Mention as an option |
| N3 | NIT | R15/R16 alternate is ±200 vs ±100 ppm/°C, besides the unverified pulse rating | Note it |
| N4 | NIT (optional) | Splitting U2/U3 between LCSC and Digi-Key is awkward at JLC | Offer global sourcing for all 40 |

Could not verify: Digi-Key pages; LCSC's own search. Repo untouched (clean before/after, 98d53a2).

### Design-agent response
| # | Action |
|---|---|
| F1 | Constraints note + Nick's sourcing policy (D26: critical parts via JLC global sourcing; passives keep the specified part with `ALT…` proposals for Sofar review, S5.h); affected rows marked † "needs constraint amendment"; Sofar's listed alternates and our own parts called out as the exceptions |
| N1–N4 | Y1, MP1–MP4, R15/R16 and U2/U3 rows updated |

---

## PR #17 (S5.f) — Round 2 (port-2 LED D10) — 2026-10-06 — APPROVED

**Reviewed:** 14452d2 vs 1f70175 (git archives).

| Claim | Result | Evidence |
|---|---|---|
| ERC 27/504: off-grid −3 (R5 group) +1 (pin-48 stub) | PASS | only endpoint_off_grid 483 → 481; all else identical |
| netcheck 51/51; midwire 0 | PASS | R5.1 on the pin-48 net with U1.48; R5.2 on ADIN_VDDIO |
| Netlist diff | PASS | pin-48 net → ADIN_P2_LED1 + D10.1; ADIN_LED_VDD + R46.2; new Net-(D10-A); nothing else (108 → 109 nets) |
| Sheet edits | PASS | +R46, D10, 3 labels, junction at a real 3-wire point, 6 wires; R5 group moved (+93.98, +91.6178); note moved |
| Pin-48 strap safety | PASS | as pin 21; P2_TX2P4_EN reads 1 with JP2 bridged or cut |
| #PWR34 / owner table | PASS | power_pin_not_driven still 8 and still names #PWR34; DESIGN owner table stays accurate |
| No raw newlines; render; docs | PASS | ≈ 13 mW with both ports active checks out (3.9 mA × 3.3 V) |

| # | Severity | Finding | Suggested fix |
|---|---|---|---|
| N1 | NIT (optional) | D25's back-power clause still says "pin 21" | "pins 21 / 48" |

Repo untouched (clean before/after, HEAD 14452d2).

### Design-agent response
N1 fixed in D25.

---

## PR #17 (S5.f) — Round 1 — 2026-10-06 — APPROVED WITH NITS

**Reviewed:** bbbbdf9 vs base 94bc4b8 (git archives): ADIN sheet, DESIGN D25 / results row / strap table, SPEC,
sofar_brief row 9, TRACKER, viewer, changelog, DEV_LOG, netcheck.md.

| Claim | Result | Evidence |
|---|---|---|
| ERC 27/508 → 27/506, only off-grid | PASS | endpoint_off_grid 485 → 483; every other item identical. Gone: #PWR49 pin, R3 pin 2, R3's wire; added: the pin-21 stub (U1's off-grid y) |
| netcheck 51/51; midwire 0; R3 unchanged | PASS | R3.1 on the pin-21 net with U1.21, R3.2 on ADIN_VDDIO |
| Netlist diff exactly as in the PR body | PASS | pin-21 net renamed ADIN_P1_LED1 + D9.1; ADIN_VDDIO + JP2.1; GND + D8.1; ADIN_LED_VDD, Net-(D8-A), Net-(D9-A); nothing else |
| Sheet edits as described | PASS | 197 → 221 items; R3 group moved (+93.98, +91.6178); nothing removed |
| Pin-21 strap safety | PASS | reads 1 with JP2 bridged (0 V across D9) or cut (no path to GND) |
| No feed from the always-on 3V3 | PASS | JP2.1 on ADIN_VDDIO only |
| LED polarity | PASS | Device:LED pin 1 K; D8.K GND, D9.K pin 21; footprint pad 1 cathode; KENTO "Green mark" at the cathode |
| Part facts | PASS | LCSC C2286/C2289 as cited; ADIN2111 Table 1 (8 mA, V_OL 0.4 V at 2 mA), Table 15 (LED_1 disabled by default), Fig. 24 |
| Arithmetic | PASS | 0.93 / 0.8 mA (≈ 0.6 mA worst case); pin 21 ≈ 1.5 mA incl. R3; ≈ 5.6 mW; 7–10× dimmer |
| No raw newlines in strings; fields/refs; render; docs | PASS | |

| # | Severity | Finding | Suggested fix |
|---|---|---|---|
| N1 | NIT | "−2 off-grid" is −3 (R3 group on grid) + 1 (pin-21 stub on U1's off-grid y) | Say so |
| N2 | NIT | "≈ 6 mW" counts only LED currents; while D9 is lit pin 21 also sinks R3's 0.7 mA (≈ 8 mW, ≈ 1.5 mA at the pin) | One clause in D25 |

Repo untouched (clean before/after, HEAD bbbbdf9).

### Design-agent response
| # | Action |
|---|---|
| N1 | Results row and changelog: "−3 with R3, its symbol and wire on grid; +1 for the pin-21 stub on U1's off-grid y" |
| N2 | D25: ≈ 1.5 mA at pin 21 incl. R3 (inside the 2 mA V_OL test point), ≈ 8 mW with link activity |

---

## PR #15 (S5.d) b153537 and PR #16 (S5.g) 585d54a — after Nick's KiCad look — 2026-10-06 — APPROVED (both)

| Claim | Result | Evidence |
|---|---|---|
| S5.d netlist identical after the move | PASS | 105 nets / 127 parts both sides; no net, pin-grouping, value, footprint or DNP change |
| ERC 27/508; netcheck 51/51 | PASS | location-stripped ERC item lists identical; netcheck report identical |
| J5 group moved +419.1 in x only | PASS | item-by-item diff (243 items each side): J5, #PWR80, #PWR81, 2 wires, note moved; J5 pins at x 485.14 |
| Note without the UrchinCam line; bus text box → "M3 threaded inserts MP1-MP4" | PASS | text and size only |
| No raw newlines inside quoted strings | PASS | quote/escape-aware scan of every .kicad_sch and nereus.kicad_sym: 0 |
| Render, docs | PASS | no overlaps; D23 + sheet layout rule, changelog, TRACKER (S6 tidy), viewer, DEV_LOG agree |
| S5.g merge brings in b153537 only + the 3D confirmation | PASS | project files = b153537; mote.pretty and tools = 73fd332; D24/TRACKER/DEV_LOG record Nick's check, which settles the rotation sign: (−90, 0, −180) is body-up |

| # | Severity | Finding | Suggested fix |
|---|---|---|---|
| N1 | NIT (optional) | The bus text box (29.21 mm wide) wraps into 5 short lines | Widen it in the S6 tidy |

### Design-agent response
N1 added to the S6 "schematic tidy" item.

---

## PR #16 (S5.g) — Round 2 — 2026-10-06 — APPROVED WITH NITS

**Reviewed:** 55e0795; delta d8a9f71..55e0795; full S5.g 8a47f71..55e0795.

| Claim | Result | Evidence |
|---|---|---|
| Insert footprint = base except opacity | PASS | diff is exactly the opacity line; pads byte-identical |
| fpextract and test restored | PASS | tools identical to base; verify 43 footprints, 0 problems |
| Library change is 3D only | PASS | the 7 stock-model additions as in round 1; nothing else |
| Nothing says the bus feeds through the insert pad | PASS | only corrected text and history lines remain |
| Q6 accuracy | PASS (nits) | matches the board (B.Cu inserts, net-less pads, front F.Cu arcs w 1.2 / r 3.03 on the BM nets) |
| D24 generic heights | PASS | |

| # | Severity | Finding | Suggested fix |
|---|---|---|---|
| N1 | NIT | The "ring" is a C-shaped ~290° arc (MP3: 279° + 11°), not a closed annulus | Say so in Q6/SPEC |
| N2 | NIT | "Under the screwed lug" is an inference (no hardware in the files) | Say "presumably" |

Repo untouched (clean before/after, HEAD 55e0795).

### Design-agent response
| # | Action |
|---|---|
| N1 | Q6, SPEC, D24 and viewer say "C-shaped arc (~290°)" |
| N2 | Q6 "which we assume the screwed lug sits on"; D24 and DEV_LOG "presumably under the screwed lug" |

---

## PR #16 (S5.g) — Round 1 — 2026-10-06 — CHANGES REQUESTED

**Reviewed:** 419c1ee vs sprint/5d-payload-connector (4fa7e4f), from a `git archive` snapshot; re-checked unchanged at
d8a9f71 (merge of the S5.d fixes).

| Claim | Result | Evidence |
|---|---|---|
| Insert footprint: pad "" → "1", opacity 0 → 1, nothing else | PASS | 2-line diff; pcbnew loads pads ['', '1'], opacity 1.0, rotate (−90, 0, −180) |
| Schematic pin "1"; netcheck skips unnumbered pads | PASS | MP1.1 BM1_P … MP4.1 BM2_N; `pcb_connectivity` skips unnumbered pads; mote MP pads ('' NPTH, '' SMD), no net, B.Cu |
| Insert model geometry | PASS | Decoded STEP byte-identical; bore r1.5, spigot r2.1 (y −1.4…0), body r3.0 (y 0…1.5), chamfer r1.75; NPTH drill 4.4 |
| 7 stock models, offset/rotation 0, files exist | PASS | load at opacity 1 |
| Orientation argument | PASS | pads at ±x; STEP centred, long axis x; all users non-polarised |
| U2/U3 no stock model; ball map | PASS | only WLP-4 P0.4 exists; DS41203 top view matches footprint and symbol |
| fpextract --verify 0 / 8 | PASS | as claimed; `renumbered()` touches only that footprint's SMD pads |
| Orientation honesty / +90 fallback | PASS | honest; the fallback is right; current values probably correct (KiCad negates model rotations; unverified) |
| ERC/netcheck unchanged | PASS | no schematic or board in the diff |

| # | Severity | Finding | Suggested fix |
|---|---|---|---|
| F1 | MAJOR (docs) | The mote doesn't feed the bus through the insert pad: each insert is on B.Cu with a net-less pad; the bus contact is a **front F.Cu ring** on the bus track (1.2 mm wide, radius 3.03 mm, ~290° around the Ø4.4 hole; MP1 BM1_P, MP2 BM1_N, MP3 BM2_P ×2 arcs, MP4 BM2_N; no vias within 3.5 mm) under the screwed lug. D24/changelog/DEV_LOG imply the feed goes through the pad; a new layout could route the bus to the back pad and drop the ring | Correct the docs to the real contact; add a layout note (replicate the ring; the back pad now carries the net too) |
| N1 | NIT | Stock model heights are generic (C_0805 1.25 mm vs 1.45 mm class; C_0603 0.8 mm vs 1.0 mm) | Note "generic heights" in D24 |
| N2 | NIT (follow-up at d8a9f71) | Viewer status line still says only "Now: S5.d" | Mention S5.g |

Repo untouched (read-only; clean before/after).

### Design-agent response
Confirmed F1 on the reference board (F.Cu arcs, r 3.03, width 1.2, on BM1_P/BM1_N/BM2_P/BM2_N around MP1–MP4). Nick
(2026-10-06): don't jump to layout details; ask Sofar first. So:

| # | Action |
|---|---|
| F1 | **Pad change reverted** (insert pad back to "" as on Sofar's board; fpextract `RENUMBER_SMD` removed, verify 0 problems with no exception). D24, SPEC (new fact: the front-ring contact), changelog, DEV_LOG, TRACKER and viewer describe the real contact. New **Sofar Q6**: is the ring-only contact deliberate, and how should a new layout copy it (ring as-is, net the insert pad too, or a ring pad in the footprint)? |
| N1 | D24: "heights are generic; use datasheet heights for potting-depth checks" |
| N2 | Viewer status line covers S5.d and S5.g |

---

## PR #15 (S5.d) — Round 1 — 2026-10-06 — APPROVED WITH NITS

**Reviewed:** 4fa7e4f vs base d5bc13b: BM_Mote_1_Master.kicad_sch, nereus.kicad_sym, DESIGN D23, SPEC, sofar_brief,
TRACKER, viewer, changelog, DEV_LOG, netcheck.md.

| Claim | Result | Evidence |
|---|---|---|
| ERC 27/508 unchanged | PASS | 535 each side; location-stripped item lists identical |
| netcheck 51/51; midwire 0; tests | PASS | J5 added to the new-parts list only |
| Netlist diff = VBUS_OUT + J5.1, GND + J5.2 | PASS | 105 nets both sides; structural diff +J5, #PWR80, #PWR81, 2 wires, 1 note, +nereus:SM02B-GHS; no other project file changed |
| nereus symbol = UrchinCam's | PASS | identical after whitespace and name normalisation; pins 1/2 passive |
| Stock footprint pads | PASS | "1" (−0.625, −1.85), "2" (0.625, −1.85), "MP" ×2 (±2.475, 1.35) |
| Pin order = UrchinCam J4/J6 | PASS | J6 pad 1 +5V, pad 2 GND; J4 pad 1 → bus-voltage input (TSR 3-2450N), pad 2 GND |
| C189893 per the UrchinCam BOM | PASS | BOM row J4/J6 → C189893 = SM02B-GHS-TB(LF)(SN) |
| Mote VBUS_OUT via P1 14/16/18 | PASS | reference board VBUS_OUT includes P1.14/16/18 |
| JST GH ratings | PASS | eGH.pdf p. 1: 1.0 A (AWG #26), 50 V, −40…+105 °C |
| Potting, render, refs, constraints | PASS | note readable and clear of wires; J5 new; no forbidden files |

| # | Severity | Finding | Suggested fix |
|---|---|---|---|
| F1 | MINOR | C189893 shows "Out of Stock" on lcsc.com today; D23/SPEC/viewer present it with no stock state | Record "LCSC stock 0 on 2026-10-06; recheck at S5.e"; optionally an alternate |
| N1 | NIT | Changelog: the MP pads are numbered "MP", not unnumbered | Reword |
| N2 | NIT | Mis-mating: GH 2-pin also carries 5 V on the UrchinCam (J6); a 5 V payload's cable fits J5 and would get 16–32 V | Layout/S6: silkscreen "VBUS 16–32 V" next to J5 |

Repo untouched (clean before/after, HEAD 4fa7e4f).

### Design-agent response
| # | Action |
|---|---|
| F1 | D23 and SPEC record "LCSC out of stock 2026-10-06, recheck in S5.e"; the S5.e TRACKER item now includes stock and names C189893 |
| N1 | Changelog reworded ("MP" mounting pads, no symbol pin, no net) |
| N2 | D23 layout note: silkscreen "VBUS 16–32 V" next to J5 |

---

## PR #14 (S5.c) — Round 2 — 2026-10-05 — APPROVED

**Reviewed:** 0c3d215 vs f97c675 (8 files: DESIGN, DEV_LOG, SOFAR_QUESTIONS, TRACKER, changelog, qe/S5.md, viewer,
test_schedit.py). Schematic and tools/schedit.py unchanged (`git diff --quiet`), so round-1 ERC 27/508, netcheck 51/51
and midwire 0 stand.

| Claim | Result | Evidence |
|---|---|---|
| F1 config.txt `gpio=24=op,dl` + `gpio=23=op,dh` | PASS | raspberrypi.com config.txt "GPIO control": op/dh/dl, applied by firmware at boot, overridable by pinctrl/Device Tree. Why GPIO24 must be driven, the POR fallback and the runtime power-off rule are added; "hog" gone; pin map row 18 and viewer fixed |
| N1 TP19 / netcheck blind spot | PASS | Results row reworded; layout note in D22 and the changelog |
| N2 Q4 state | PASS | `[-]` |
| N3 imports | PASS | merged; test_schedit OK |
| Saved report / tracker / viewer | PASS | faithful; TRACKER [x]; viewer "your KiCad look" |

| # | Severity | Finding | Suggested fix |
|---|---|---|---|
| N4 | NIT (optional) | The RPi page notes "a delay of a few seconds between power being applied and the changes take effect"; the ADIN stays off meanwhile (R43) | One phrase to make the timing explicit |

Repo untouched (clean before/after, HEAD 0c3d215).

### Design-agent response
| # | Action |
|---|---|
| N4 | Boot order step 1: "applied a few seconds after power-up (the ADIN is held off by R43 until then)" |

---

## PR #14 (S5.c) — Round 1 — 2026-10-05 — APPROVED WITH NITS

**Reviewed:** f97c675 vs base 31bc0f3: BM_Mote_1_Master.kicad_sch, tools/schedit.py + test, DESIGN, SPEC, TRACKER,
SOFAR_QUESTIONS, sofar_brief, viewer, changelog, DEV_LOG, netcheck.md. ADIN2111 PDF hash matches SPEC.

| Claim | Result | Evidence |
|---|---|---|
| Sheet change is only what's listed | PASS | Item-by-item compare (223 → 237 items): −R10; +R26, R27, R43, #PWR77/78/79, 3 labels, 6 wires; lib_symbols −R10's, +2 imported, shared ones byte-identical. No other project file changed |
| ERC 27/508 unchanged | PASS | 535 each side; ercsum and location-stripped item lists identical |
| netcheck 50/50 → 51/51 | PASS | Copper I2C1_SCL/SDA gain a second shared pin (+2); copper ADC1_IN16 now TP19 alone (−1) |
| midwire 0; tests | PASS | All tool tests OK incl. CloneTest |
| Netlist diff exactly as described | PASS | I2C1_SCL +R26.1; I2C1_SDA +R27.1; 3V3 +R26.2, R27.2; ADIN_PWR +R43.1; GND +R43.2; R10 gone; TP19 joins SW_EN |
| R26/R27 fields = mote | PASS | 34 fields; only Footprint (`Vault:` prefix, D19) and SHEET differ; flags match |
| Mote copper | PASS | ADIN_PWR = {TP8, U2.B2, U3.B2, U8.6} (no pull); I2C1 nets incl. R26/R27; R10 SW_ON ↔ ADC1_IN16; strap resistors as tabled |
| Strap table vs ADIN2111 Rev. B | PASS | Table 8/22, Table 3, 90 ms, abs max VDDIO + 0.3 V all match |
| AP22913 facts | PASS | DS41203 Rev. 6-2; "no internal pull-down" is a fair inference (≤ 1 µA leakage at 0 V and 5.25 V) |
| Pi I²C pull-ups | PASS | Reduced schematic R23/R24 1.8K 1 % to 3V3 |
| BCM2835 §6.2 | PASS (as caveated) | GPIO0–8 High; BCM2710A1 caveat in SPEC |
| Arithmetic | PASS | 1.302 kΩ, 2.23 mA, 967 Ω, 272 pF, 0.1 V, 33 µA, ≈ 1.8 mA, ≈ 0.57 mA |
| Render | PASS | Readable, no overlaps |
| Hard constraints | PASS | No .kicad_pcb / reference / Archive changes; J1.1/17 unchanged |

| # | Severity | Finding | Suggested fix |
|---|---|---|---|
| F1 | MINOR | Boot order step 1 / viewer: the Pi's GPIO24 default pull-down "holds reset" only while the ADIN is unpowered; once ADIN_PWR is high, the ADIN's internal RESET pull-up fights a weak BCM pull-down (neither value published), so the level is undefined unless GPIO24 is driven. The GPIO23 hog powers the ADIN while GPIO24 is still an input. Harmless (POR resets it; straps read correctly), but steps 1/4 don't describe reality | Drive GPIO24 low before ADIN_PWR (e.g. config.txt `gpio=24=op,dl`, `gpio=23=op,dh`), or say POR makes steps 1/4 optional and pulse RST after the SPI driver loads; fix the viewer |
| N1 | NIT | Results row says "kept parts' connections identical" but TP19 (kept) moved; netcheck can't see it (TP19's copper net is TP19 alone, copper SW_ON has no shared parts). Layout needs a new TP19 → SW_EN trace | Reword; add the layout note to the changelog / D22 |
| N2 | NIT | SOFAR_QUESTIONS Q4 state `[~]` isn't in the state key | Use `[-]` or extend the key |
| N3 | NIT | test_schedit.py has two `from midwire import` lines | Merge |

**Note:** ADIN CS, SCLK and SDI have internal pull-downs (Table 8). With the ADIN powered and the Pi off, CS would
read selected and SDO could drive into an unpowered GPIO9. R43 prevents that: a further reason for D21.

**Could not verify:** internal pull values (ADIN RESET pull-up, BCM pad pulls); the BCM2710A1 pull table.
Repo untouched (clean before/after, HEAD f97c675).

### Design-agent response
| # | Action |
|---|---|
| F1 | Option (a): boot order step 1 is now config.txt `gpio=24=op,dl` + `gpio=23=op,dh` (firmware applies them before the kernel; the kernel/user space can still change the pins — Raspberry Pi documentation, config.txt "GPIO control"); explains why GPIO24 must be driven; notes POR covers a missed step (then pulse RST after the SPI driver loads). "GPIO hog" replaced throughout; pin map and viewer fixed |
| N1 | Results row: "identical except TP19 (D22)" + why netcheck can't see it; layout note (route TP19 → SW_EN where R10 was) added to D22 and the changelog |
| N2 | Q4 → `[-]` (deferred, context only) |
| N3 | Imports merged |

---

## S5.b (local commit 80b967a; PR not yet open) — Round 1 — 2026-10-05 — APPROVED WITH NITS

**Reviewed:** commit 80b967a on sprint/5b-pi-header-wiring vs base 9949b37: BM_Mote_1_Master.kicad_sch,
tools/schedit.py + test, DESIGN, TRACKER, viewer, changelog, DEV_LOG, draft PR body.

| Claim | Result | Evidence |
|---|---|---|
| ERC 74/508 → 27/508: −29 pin_not_connected, −18 label_dangling | PASS | Fresh ERC on git-archived base and head: 582 → 535. pin_not_connected 39 → 10 (FID1–6, MTG1–4 remain), label_dangling 18 → 0; power_pin_not_driven 8 and unresolved_variable 9 unchanged |
| Warnings unchanged in count and type | PASS | 508 both: off_grid 485, multiple_net_names 12, unconnected_wire_endpoint 11; new stubs/labels add no off-grid |
| Netlist: each of 11 nets gains exactly its J1 pin; renames | PASS | 117 → 106 nets. ADIN_INT +J1.22, MISO +J1.21, MOSI +J1.19, NSS +J1.24, PWR +J1.16, RST +J1.18, SCK +J1.23, I2C1_SCL +J1.5, I2C1_SDA +J1.3; `Load Switch/SW_ON` → `SW_EN` +J1.36, `Load Switch/SW_FLAGB` → `SW_FLAGB` +J1.38; 11 `unconnected-(J1-…)` nets absorbed; nothing else changed |
| Pin map = Pi Zero 2 W GPIO numbering | PASS | J1 pin names in the netlist agree with the DESIGN and viewer pin maps |
| 17 no-connect flags; pins 1/17 untouched | PASS | Diff adds 17 no_connect, 12 wires, 13 labels, 0 junctions, removes nothing; 11 + 17 = all 28 GPIO; no NC ERC errors |
| SW_EN / SW_FLAGB labels | PASS | SW_EN = R10.1, R42.1, U11.4, J1.36; SW_FLAGB = R35.1, TP35.1, U11.9, J1.38 |
| netcheck 50/50; midwire 0; tests | PASS | netcheck report identical below header; all tool tests OK incl. the 180° label assertion |
| schedit 180° labels | PASS | Code and test agree; render shows left labels reading leftward, no overlaps |
| Render | PASS | J1 stubs, labels and NC X's as claimed; Load Switch SW_EN/SW_FLAGB labels |
| Hard constraints | PASS | No .kicad_pcb, reference-design or Archive/ files touched; Pi 3V3 not connected |
| Docs | PASS (2 nits) | Numbers agree across DESIGN, TRACKER, viewer, changelog, PR body |

| # | Severity | Finding | Suggested fix |
|---|---|---|---|
| N1 | NIT | DEV_LOG: no `---` separator between the S5.b and S4.d entries | Add `---` |
| N2 | NIT | DEV_LOG names a specific VBUS label for the changed multiple_net_names line; in the QE's runs it was PHY2_P/BM2_P — KiCad's cited example varies run to run | Reword generically |

**Risk to carry into S5.c (not a defect here):** Pi GPIO now reach parts on separately switched rails. GPIO8/CE0
(ADIN_NSS) defaults to a pull-up at Pi reset (BCM283x convention, not re-verified) and SPI0 idles CS high — either can
back-power the ADIN2111 through its IO clamps while ADIN_PWR (GPIO23, default pull-down) keeps ADIN_VDDIO off. R35
(100 kΩ to shield 3V3) feeds GPIO20 when the Pi is off (≈ 33 µA). The Pi's I²C pull-ups go to Pi 3V3 while U4 is on
shield 3V3. ADIN_RST on GPIO24 (default pull-down) holding the ADIN in reset at boot is in our favour.

**Could not verify:** RP3A0 GPIO reset-default pulls from a primary source; the design session's own check.sh output
(independent ERC/netcheck reproduces the counts). Repo untouched (clean before/after, HEAD 80b967a).

### Design-agent response
| # | Action |
|---|---|
| N1 | Separator added |
| N2 | Reworded: "one multiple_net_names line cites a different example label; count and type unchanged (ERC text varies run to run)" |
| Risk | Added to TRACKER's S5 pull-up-rail/sequencing item (CE0 default-high, R35 → GPIO20, Pi I²C pull-ups on Pi 3V3) and the viewer |

---

## PR #11 (S5.a) — Round 2 — 2026-10-05 — APPROVED WITH NITS

*Same standing S5 QE session. Reviewed `eef10dc`.*

**Claims checked, all PASS:** F1 R34 PART NUMBER; F2 R42 10 kΩ (worst case holds under both
pull-up models; Pi load 0.33 mA; 3.3 V > V(SHUTR) max, ≤ 6 V ROC; no stale 100 kΩ); F3 RTN = GND
recorded; F4 N6 closed (figures match); F5 stale docs fixed; N1–N4; ERC 74/626 item list unchanged;
connectivity vs round 1 identical (117 nets, 124 parts; only R41/R42 values); vs base as claimed;
netcheck 50/50, midwire 0, tests OK; render; docs consistent.

| # | Severity | Finding | Evidence | Suggested fix |
|---|---|---|---|---|
| N5 | NIT | D18 says a > 20 µF payload "still starts, via auto-retry"; it charges in current limit directly (100 µF × 32 V / 0.73 A ≈ 4.4 ms ≪ tCL(dly) 512 ms); auto-retry only if TSD trips | §9.3.5.1 | Reword |

**Could not verify:** "FPF2700 had none" (reverse-input protection; no FPF2700 datasheet in the
QE session — it doesn't affect the decision); potted thermal; JLC Basic/Extended; Pi GPIO16 reset
pull-down; 32 V hard short explicitly.

**Repo untouched:** clean before and after, HEAD eef10dc.

### Design-agent response

| # | Action |
|---|---|
| N5 | D18 reworded: charges in current limit (≈ C·V/0.73 A, e.g. 4.4 ms for 100 µF at 32 V, inside tCL(dly) 512 ms); auto-retry only if thermal shutdown trips |
| FPF2700 reverse protection | The FPF2700 datasheet (Rev. 1.0.3) describes a single N-channel MOSFET with no reverse-input protection feature, consistent with D18 |

---

## PR #11 (S5.a) — Round 1 — 2026-10-05 — CHANGES REQUESTED

*Fresh S5 QE session. Reviewed `beae5a8` against base `1f906bc`. Findings verbatim;
claims summarised (full text in the QE session's transcript).*

**Claims checked (summary), all PASS:** symbol pins = TI Table 6-1; Texas_DRC0010J pads
1–10 + EP "11" match TI's DRC0010J outline; I_LIM 0.73 A (Eq. 3, I(OL) table; with ±1 %
R ≈ 0.68–0.77 A); R41/OVP/dVdT per pin table, §9.3.1–9.3.3, Fig. 10-14; C49/C50 ≥ 0.01 µF
ROC, D3 is TI's output Schottky; thermal ≈ 0.25–0.37 W, ≈ 11–16 °C rise; reverse-current
blocking (improvement on the mote); LCSC C1848341 8,068 in stock, TI ACTIVE; ERC 74/626
item diff; kept parts' connectivity identical, new nets as listed; R11 dnp; netcheck
50/50, midwire 0, tests OK; render OK; hard constraints OK; docs numbers agree.

| # | Severity | Finding | Evidence | Suggested fix |
|---|---|---|---|---|
| F1 | MAJOR | R34's PART NUMBER field still says RC0402FR-07374KL (374 kΩ); only Value and Description were updated. A BOM built from PART NUMBER would order 374 kΩ: outside TI's 7.5–267 kΩ ROC, I_LIM ≈ 18 mA, payload never starts | Load sheet R34 fields | Set PART NUMBER = RC0402FR-079K09L |
| F2 | MAJOR | R42 = 100 kΩ doesn't guarantee payload off by default at datasheet limits: I(SHDN) at 0.4 V is −2.4 typ / −10 µA max; V(SHDN) open 2.39–3.1 V; V(SHUTF) min 0.9 V, V(SHUTR) max 1.8 V. Worst case ≈ 0.8–1.0 V vs 0.9 V guaranteed-off: no margin. The Pi's GPIO pull-down helps only with a powered Pi fitted | SLVSDT4F §7.5 LOW IQ SHUTDOWN rows | R42 → 10 kΩ (e.g. RMCF0402FT10K0): worst case ≤ 0.1 V; cite the rows in D18 and SPEC |
| F3 | MINOR | RTN tied to GND isn't recorded; §10.4 says "Do not connect RTN to GND" (disables reverse-input protection) while §12.1 allows RTN/GND/PowerPAD together without reverse protection. Correct here, but a reviewer reading §10.4 will flag it | Netlist GND: U11.3/5/6/11 | One line in D18, SPEC and sofar_brief row 5 |
| F4 | MINOR | TRACKER's "Replace U9" is ticked but its N6 sub-check (output cap / hard short up to 32 V; C50 100 nF) isn't recorded as closed. Data exists: C_OUT ROC ≥ 0.01 µF, start-up into short (Fig. 9-12), fast-trip 1.6 A / 220 ns, TSD 155 °C with 512 ms auto-retry, D3 Schottky (§11.1) | TRACKER S5 | Add a sentence closing N6 with citations |
| F5 | MINOR | Stale docs: SPEC confirmed facts still "load switch is U9 FPF2700MX; R34 374 kΩ"; FPF2700 fact not marked superseded; DESIGN hierarchy "U9 24 V payload switch"; SPEC back-feed text "payload port via R11" | grep | Update; mark FPF2700 historical |
| N1 | NIT | Footprint-link accounting is −4 (U9, R32, R33, TP34) +1 (R42 keeps R32's library-less footprint) = −3, not "U9/R33/TP34" | erc.rpt diff | Reword; R42 joins the S4.d list |
| N2 | NIT | R41 conventions: Value "1M" vs MPN-as-Value elsewhere, "MPN" vs "PART NUMBER", stock IEC graphic; U11 has LCSC, R34/R41/R42 don't | field dump | Harmonise before the S6 BOM |
| N3 | NIT | dVdT floating (≈ 36 V/ms): payload input capacitance above ≈ 20 µF starts in current limit (works via 512 ms retry/TSD), no tuning option | §9.3.3, §10.2.2.4 | Optional DNP C_dVdT footprint, or state a max payload capacitance |
| N4 | NIT | sofar_brief row 5: add R_ON 478 vs 88 mΩ (0.35 V at 0.73 A) and RTN = GND; qualify "R11 fitted" as "in the files we received"; power_budget §1 still describes U9 | sofar_brief, power_budget | — |

**Could not verify:** potted thermal; JLC Basic vs Extended class; Pi GPIO16 reset
pull-down (primary source); 32 V hard short explicitly (TI figures at 24 V).

**Repo untouched:** clean before and after, HEAD beae5a8.

### Design-agent response

| # | Action |
|---|---|
| F1 | R34 PART NUMBER = RC0402FR-079K09L (Value already). Also checked R41/R42 fields |
| F2 | R42 → **10 kΩ RMCF0402FT10K0** (RESISTANCE 10kR, description with the worst-case math). D18 and SPEC cite I(SHDN) −10 µA max, V(SHUTF) min 0.9 V, V(SHUTR) max 1.8 V. Render checked |
| F3 | D18, SPEC facts and sofar_brief row 5 record RTN = GND (§12.1; §10.4 applies only when reverse protection is wanted). Verified both passages in SLVSDT4F |
| F4 | D18 and TRACKER close N6 (C_OUT ≥ 0.01 µF, Fig. 9-12, fast-trip 1.6 A / 220 ns, TSD 155 °C / 512 ms, D3 per §11) — figures verified in SLVSDT4F |
| F5 | SPEC confirmed fact now U11/9.09 kΩ/R11 DNP; FPF2700 fact marked historical; DESIGN hierarchy U11; back-feed text "through U11 when SW_EN has it on" |
| N1 | DESIGN warnings text: −4 +1; R42's library-less footprint is covered by S4.d |
| N2 | R41: Value and PART NUMBER = RC0402FR-071ML, MPN field dropped, RESISTANCE "1MR" shown (Value hidden, like the imported resistors). Graphic left as stock; LCSC fields for the resistors deferred to the S6 BOM (not invented) |
| N3 | D18 states the limit: payload input capacitance above ≈ 20 µF starts in current limit (still starts via auto-retry). No C_dVdT footprint added |
| N4 | sofar_brief row 5 adds R_ON and RTN = GND, and "in the files we received (Q2)"; power_budget §1 marks the FPF2700 analysis superseded by D18 |
