nickraymond/nereus_Pi_shield_ADIN2111/docs/design-review/qe/S4.md

# QE reviews — S4 (PR #8 S4.a, PR #9 S4.b, PR #10 S4.c, PR #12 S4.d)

*Reports from the standing S4 Quality Engineer session, sent straight to the design
session and saved by the design agent. Newest round first. Design-agent responses
follow each round.*

---

## PR #12 (S4.d) — Round 2 — 2026-10-05 — APPROVED

*Same standing S4 QE session. Reviewed `40ff662`. The QE's send was paused by the
session-message limit, so the design agent read the report from the QE transcript.
Round-1 N4 was withdrawn by the QE (D19's cell is complete).*

**Claims checked, all ✅:** placed-pad verifier as claimed (head: 43 footprints, 0
problems); the QE's own mirrored-INA232 test is caught ("vs U4 (back): placed pad
positions differ"); re-extraction changed only each file's Value line (ignoring uuids,
42 of 43 files); no schematic change, ERC 74/508, netcheck 50/50, tests pass; KiCad's
library-parity check re-run against the new library: still 58 of 150 instances
(matches D19, PR and viewer); F1/N3 docs (source-instance wording, DRC/"Update from
Library" warning, TRACKER S6 and viewer attribute/courtyard items).

**Findings:** none.

**Could not verify:** a real DRC on Nick's board (no board writes; in-memory parity check instead).

**Repo untouched:** clean before and after, HEAD 40ff662.

---

## PR #12 (S4.d) — Round 1 — 2026-10-05 — APPROVED WITH NITS

*Same standing S4 QE session. Reviewed `34e004f` against base `10d64d0`. Findings
verbatim; claims summarised.*

**Claims checked, all ✅:** verify 0 problems; ERC 74/508 (no footprint_link_issues; base
74/626); netcheck/midwire/tests; netlist identical except 117 footprints bare → Vault:;
118 fields; vault_footprints.txt complete; **flip/orientation**: for all 150 board
instances the library footprint placed like the instance (flipped if back) matches pad
centres within 10 nm, incl. the standoff's swapped front/back padstack; 3D models travel
as embedded files.

| # | Severity | Finding | Evidence | Suggested fix |
|---|---|---|---|---|
| F1 | MINOR | KiCad's `FootprintNeedsUpdate` (behind DRC's "doesn't match library") flags 58 of 150 instances against the new library — graphics only (Altium-import per-instance variation on User/Fab layers; Hole_M3 keepouts written B/F swapped and pad drops `zone_layer_connections`). F8 re-link unaffected; expect ~58 lib_footprint_mismatch DRC warnings; "Update Footprints from Library" would rewrite Fab/User graphics | own script, 54 graphics-only + 4 Hole_M3 | Note in D19/PR; don't update kept parts from library; correct "layer-for-layer" (holds for the source instance only) |
| N1 | NIT | The shipped verifier checks back-side instances only with a mirror-invariant distance multiset, so it can't detect a wrong-chirality library | fpextract.verify | Place the lib copy like the instance (SetParent, Flip TOP_BOTTOM, orientation, position) and compare pad centres |
| N2 | NIT | Library Value fields carry the source instance's part value | mote.pretty | Set Value to the footprint name |
| N3 | NIT (layout) | No footprint type attribute (0 `attr` on the board and library) → SMD-only position files drop parts; no courtyards (on User layers). Pre-existing | grep | Note for S6/layout |
| N4 | NIT | Check D19's rationale cell ends with the F8 claim | DESIGN D19 | — |

**Could not verify:** a real DRC against Nick's board (no board writes; used the parity function in memory).

**Repo untouched:** clean before and after, HEAD 34e004f.

### Design-agent response

| # | Action |
|---|---|
| F1 | D19 and the PR now say to expect ≈ 58 graphics-only DRC mismatch warnings and not to run "Update Footprints from Library" on kept parts; viewer layout list has the item; "layer-for-layer" corrected (source instance) |
| N1 | `verify` now places a copy of the library footprint like each instance (SetParent, Flip TOP_BOTTOM for back, orientation, position) and compares pad centres by number: still 0 problems; a deliberately mirrored INA232 footprint is caught ("vs U4 (back): placed pad positions differ") |
| N2 | `extract` sets Value to the footprint name; library re-extracted (43 files) and re-verified: 0 problems |
| N3 | TRACKER S6 item and viewer layout item (set SMD/THT attributes and courtyards before fab outputs) |
| N4 | D19's cell ends with the F8 rationale and verification (checked) |

---

## PR #10 (S4.c) — Round 4 — 2026-10-05 — APPROVED WITH NITS

*Same standing S4 QE session. Reviewed `c207aab`.*

**Claims checked, all ✅:** constraint 7 amended by Nick as quoted, D12/D17/DEV_LOG
cross-referenced; D14 wording (N7); viewer status (N8); still docs only (705 = 76/629).

| # | Severity | Finding | Evidence | Suggested fix |
|---|---|---|---|---|
| N9 | NIT | Three current-state summaries still say the power path is unchanged / "exactly as Sofar built it" without the D17 exception: SPEC goal (lines 10–11), README line 5, viewer Rating line | grep | Add "(except the payload load switch, D17)" |

**Repo untouched:** clean before and after, HEAD c207aab.

### Design-agent response

| # | Action |
|---|---|
| N9 | Fixed in all three |

---

## PR #10 (S4.c) — Round 3 — 2026-10-05 — CHANGES REQUESTED

*Same standing S4 QE session. Reviewed `8d92b8a`. Findings verbatim; claims summarised.*

**Claims checked (summary), all ✅:** still docs only; F4 consistent across D17,
power_budget, SPEC, Q2, TRACKER, viewer, DEV_LOG, with the edit deferred to S5; N6 in the
S5 criteria; Digi-Key status accepted from the design agent's direct read; viewer in sync.

| # | Severity | Finding | Evidence | Suggested fix |
|---|---|---|---|---|
| F5 | MAJOR | D17 conflicts with SPEC hard constraint 7 ("no part in it (L1/L2, D1–D3, U9/R34/R11, R8, …) changes value or part number"). D17 makes R11 DNP and replaces U9 (possibly re-deriving R34/R33/R35). Hard constraints are absolute; Nick must amend it explicitly. QE's miss in round 2 | SPEC constraint 7; DESIGN D17; TRACKER S5 | With Nick's explicit approval, amend constraint 7 (payload load switch excepted); reference D17 in D12/constraint 7; record in DEV_LOG |
| N7 | NIT | D14's back-feed text says "the payload port via R11"; with R11 DNP it's only through U9 when SW_EN has it on | DESIGN D14 | Update wording |
| N8 | NIT | Viewer status line still says "Next: QE round 2" | viewer | Update |

**Repo untouched:** clean before and after, HEAD 8d92b8a.

### Design-agent response

| # | Action |
|---|---|
| F5 | Asked Nick; he approved the amendment as written. SPEC constraint 7 now: "…except the payload load switch: R11 is DNP and U9 (obsolete) is replaced by a function-equivalent part, with R34/R33/R35 re-derived as needed (D17). L1/L2, D1–D3, R8, C22/C23/R15/R16 etc. stay unchanged. (Amended by Nick, 2026-10-05.)" D12 notes the exception; D17 says it amends constraint 7; DEV_LOG records it |
| N7 | D14 wording updated (via R11 as captured, or through U9 when SW_EN has it on once R11 is DNP) |
| N8 | Viewer: "Next: QE round 4, then your review" |

---

## PR #10 (S4.c) — Round 2 — 2026-10-05 — CHANGES REQUESTED

*Same standing S4 QE session. Reviewed `30e2405` against base `11914fb`. Findings
verbatim; claims summarised.*

**Claims checked (summary), all ✅:** still docs only (705 = 76/629); F1 12 W column,
F2 VBUS quadratic, F3 caveats/ψJT/§7.3 note 5 and N1–N5 all recomputed or confirmed;
FPF2700 facts confirmed against all 19 pages (Table 1 lists 374 kΩ → 0.59/0.74/0.89 A);
D15–D17, Q3, S5 capture and viewer consistent.

| # | Severity | Finding | Evidence | Suggested fix |
|---|---|---|---|---|
| F4 | MAJOR | D17 and power_budget §1/§2 say the payload port has U9's ≈ 0.74 A limit, but in this schematic R11 (0 Ω across U9, VBUS ↔ VBUS_OUT) is fitted (in_bom yes, dnp no). As captured U9 is bypassed: no limit, and SW_EN can't switch the payload off. Matters for S5 (SW_EN → Pi pin 36). The docs treat R11 only as Sofar's production question (Q2), but our BOM is what gets built | Master R11: in_bom yes, dnp no; netlist VBUS has R11.1 and U9.1, VBUS_OUT has R11.2 and U9.8 | Say it plainly in D17 and power_budget §1/§2; add a TRACKER S5 item for Nick's decision before the U9 replacement: R11 DNP (switch active, limit, SW_EN works) or fitted (always on, unlimited); keep Q2 as context |
| N6 | NIT | For the U9 replacement: FPF2700 Table 2 asks C_OUT ≥ 22 µF (24 < VIN ≤ 27 V) / ≥ 47 µF (27–32 V) for hard shorts above 24 V; Eq. 2 caps C_OUT ≤ I_LIM_MIN · 500 µs / V_OUT (≈ 9 µF at 32 V with 0.59 A), so they conflict at 32 V for this R_SET. The mote has only C50 = 100 nF on VBUS_OUT; R11 fitted may be why Sofar never hit this | FPF2700 Rev. 1.0.3 p. 14; netlist C50 | Add output-cap / hard-short behaviour up to 32 V to the replacement criteria |

**Could not verify:** Digi-Key status/LTB dates (Digi-Key blocks automated reads; Nick has
the page); ADI 77 mW and USB Table 7-7 as before.

**Repo untouched:** clean before and after, HEAD 30e2405.

### Design-agent response

| # | Action |
|---|---|
| F4 | Verified: R11 in_bom yes / dnp no in our schematic, and a normal fitted footprint on the reference board. Asked Nick: **R11 DNP, use the load switch** (D17 rewritten). power_budget §1/§2 state "as captured R11 is fitted and bypasses U9"; TRACKER S5 has "R11 → DNP" before the U9 replacement (schematic edit belongs to S5); Q2 kept as context |
| N6 | Added to the S5 U9-replacement criteria (TRACKER, viewer) |
| Digi-Key status | Read directly by the design agent in the browser pane: "Part Status: Obsolete — This product is no longer manufactured" |

---

## PR #10 (S4.c) — Round 1 — 2026-10-05 — CHANGES REQUESTED

*Same standing S4 QE session; sent straight to the design session. Reviewed `bc19543`
against base `11914fb`. Findings verbatim; claims summarised.*

**Claims checked (summary), all ✅:** docs only, check.sh unchanged; every §2 bus cell,
§3 loss/ΔTj cell, §4 IPC-2221 figure and §5 R38 corner recomputed exactly; RPi docs
(via the raspberrypi/documentation repo source), product brief, TI §7.4/§7.5 confirmed;
Fig 7-2 reading within ±2 points and slightly conservative; "57 footprints" = 57 unique
IDs (167 instances); docs in sync.

| # | Severity | Finding | Evidence | Suggested fix |
|---|---|---|---|---|
| F1 | MAJOR | The budget never compares against the Bristlemouth v1 per-module limit (≤ 12 W from a nominal 24 V bus, a SPEC confirmed fact); only the 890 mA / 21.4 W inductor rating. Against 12 W, shield + 1 A Pi (5.83 W) leaves 6.2 W for payload, not 15.5 W; a 2 A Pi leaves 0.5 W. Whether the host can supply more than 12 W isn't addressed | SPEC line 53; arithmetic | Add the 12 W limit as a second budget line; state which limit governs; put to Nick with P-S4c-1 or SPEC open questions; adjust the readings |
| F2 | MINOR | PoDL inductor drop and dissipation missing: SRF1260-101M series DCR 0.656 Ω max; at 890 mA L1 drops 0.58 V (VBUS ≈ 15.4 V on a 16 V bus, ~4 % more input current) and dissipates 0.52 W of shield heat | SPEC (SRF1260); netlist VBUS includes L1.1 | Compute the 16 V rows at VBUS = 16 V − I·0.656 Ω; list L1's I²R as shield heat |
| F3 | MINOR | Thermal caveats missing: (a) TI says this RθJA is for comparison only and points to a section absent from SLUSEF4A; (b) Fig 7-2 is at 25 °C, RDS(on) rises when hot; (c) lifetime-derating note is §7.3 note (5), not "§7.1 note" | SLUSEF4A p. 4–5 | Say ΔTj is indicative; quantitative bench item Tj ≈ T_top + ψJT·P (ψJT 9.3 °C/W); fix the citation |
| N1 | NIT | The 1 A "assumed" load can be partly sourced: Camera Module 250 mA, HDMI 50 mA, GPIO 50 mA (RPi docs) → ≈ 600–700 mA before USB devices | power-supplies.adoc | Cite it to support P-S4c-1 |
| N2 | NIT | Product brief: Pi operating temperature −20 °C to +70 °C, relevant in a sealed housing next to U10 | product brief | One line in §3 |
| N3 | NIT | Middle option for P-S4c-2: R38 = 13.5 kΩ (E192) → 5.04 V nominal, 4.88–5.21 V; and at the 13.7k low corner, load regulation + header drop leave only ~30–50 mV above the 4.75 V bench threshold | arithmetic; Fig 7-4 | Optional row in §5 |
| N4 | NIT | "57 footprints" → 57 footprint IDs (167 instances) | reference .kicad_pcb | Reword |
| N5 | NIT | Fig 7-2's legend duplicates "PFM, VIN=24V"; footnote it | page 7 | Footnote in §1 |

**Could not verify:** ADI product page (timed out for the QE too; allowance is labelled);
USB 2.0 Table 7-7 and IPC-2221 constants (standard values, not re-fetched).

**Repo untouched:** clean before and after, HEAD bc19543.

### Design-agent response

| # | Action |
|---|---|
| F1 | §1 now lists both limits; §2 has a "12 W limit: left for payload" column (6.2 W at the 1 A target). New reading: U9's ≈ 0.74 A limit (FPF2700 datasheet, supplied by Nick) doesn't enforce a 12 W budget → Nick decided (D17): payloads are small devices; payload port kept as Sofar designed, no extra enforcement; 12 W shown for information |
| F2 | §2 solves I·(bus − 0.656·I) = P for every row (VBUS shown); L1 heat in §2 (39 mW at the shield's own 245 mA; 0.52 W / 0.58 V at 890 mA) |
| F3 | §3 states ΔTj is indicative (comparison RθJA, 25 °C efficiency, potting); bench item Tj ≈ T_top + 9.3 °C/W · P_U10 (≈ +5 °C at 0.53 W); citation now §7.3 note 5 |
| N1 | Cited (verified on the RPi page): typical + camera + GPIO ≈ 650 mA, added as a row; D15 records it |
| N2 | §3 line added |
| N3 | §5 table now shows 13.7 / 13.5 / 13.3 kΩ; Nick had already chosen 13.7 kΩ (D16); 13.5 kΩ recorded as the drop-in fix if the bench check fails |
| N4 | TRACKER and viewer reworded |
| N5 | Footnote in §1 |
| Also | Nick's decisions D15 (Pi ≤ 1 A) and D16 (R38 13.7 kΩ) recorded; FPF2700 facts added (Sofar Q3 answered from the datasheet); at Nick's request, lifecycle check: **FPF2700MX is obsolete** (Digi-Key) → captured in S5 for Nick, plus a whole-BOM lifecycle check before S6 |

---

## PR #9 (S4.b) — Round 2 — 2026-10-05 — APPROVED

*Same standing S4 QE session; report sent straight to the design session. Reviewed
`c18ccfc` (18676fe + c18ccfc on 658bd7d), base `b394edb`.*

**Claims checked (summary), all ✅:** check.sh 705 = 76/629, netcheck 53/53, midwire 0,
tests 7/4/12/5; no connectivity change since round 1; F1 primary source independently
fetched (RPI-ZERO2W_R1: power micro-USB J1 pin 1 → 5V with only C1, J8 pins 2/4 on 5V,
data port not drawn) and Nick's decision recorded with the mechanism consistently in
D14, SPEC, note, bench list and S4.c budget; F2 note cites D14 (render clear); F3 demo
line matches the netlist; F4 rename complete (file, name, Value, field, netlist; matches
the stock filter; loads; no old name left); F5 dead branch removed; F6 cut guidance;
docs and viewer in sync.

**Findings:** none.

**Could not verify:** net-tie DRC acceptance (needs the footprint on a board: Nick's first
DRC); Pi Zero 2 W data-port VBUS wiring (recorded open; the bench rule covers it).

**Repo untouched:** clean before and after, HEAD c18ccfc.

---

## PR #9 (S4.b) — Round 1 — 2026-10-05 — CHANGES REQUESTED

*Same standing S4 QE session (new PR in the sprint); report sent straight to the design
session. Reviewed `658bd7d` against base `b394edb`. Findings verbatim; claims summarised.*

**Claims checked (summary), all ✅:** ERC 78/629 → 76/629 with exactly J1 Pin 2's two
errors removed; existing connections identical (only the pins-only net renamed to
PI_5V); netcheck 53/53; midwire test fails on base tools, passes on head; Master diff
only the intended additions, 0 duplicate uuids; JP1 is the stock symbol (structural
compare), not in BOM; footprint pads and courtyard identical to the reference board's
R11; bridge overlaps both pads, mask exposes it, no paste, net tie, excluded from
BOM/pos; footprint loads (fp export svg; footprint_link_issues unchanged); layout clean;
viewer in sync; hard constraints OK.

| # | Severity | Finding | Evidence | Suggested fix |
|---|---|---|---|---|
| F1 | MAJOR | D14's safety reasoning ("never USB-power the Pi with JP1 bridged") doesn't record the failure mechanism and misses the most likely trigger. (a) On the Pi Zero family the micro-USB data port's VBUS also feeds the 5 V rail (confirm with the Zero 2 W schematic), so a laptop for USB-gadget/serial setup ties a host's 5 V to 5V_PI. (b) Shield unpowered: that 5 V back-feeds through L6 and U10's high-side MOSFET body diode (SW→VIN) onto VBUS, which joins L1.1, U5, U9, R8 and R11→VBUS_OUT: ~4.4 V from a laptop onto the bus side and the payload connector. (c) Shield powered: 5V_PI drives the laptop's VBUS; two supplies fight; U10 (PFM) won't sink. D5's "open by default" protected against all of this; D14 replaces it with a procedure and defers the hardware guard | netlist VBUS members; synchronous-buck body-diode reverse path; D14/SPEC text | No schematic change needed if Nick keeps D14: (1) write the back-feed paths into D14 and SPEC; (2) Nick re-confirms D14 knowing this; (3) bench item and schematic note say *any* USB cable (power or data) requires JP1 cut. Otherwise consider a reverse-blocking guard (ideal diode / load switch on 5V_PI) in this revision |
| F2 | MINOR | The schematic note cites "(D5)"; should be D14 | Master text at (106.68, 30.48) | "(D14)"; add "or a USB data cable" |
| F3 | MINOR | TRACKER S4 Demo line still S4.a's (Errors 78, 5V_PI pins); "S4.a converter (this PR)" stale | TRACKER S4 block | Update to S4.b expectations |
| F4 | NIT | Stock symbol's ki_fp_filters "SolderJumper*Bridged*" hides `R_1210_Bridged_NetTie` in the footprint chooser | Jumper.kicad_sym | Rename e.g. `SolderJumper-2_R1210_Bridged_NetTie`, or note it |
| F5 | NIT | The new skip branch in `lib_pins` can't trigger (only prefixed top-level symbols are iterated) | lib_pins output | Delete the branch or fix its comment |
| F6 | NIT | Cutting a 1.0 mm exposed bridge needs two cuts and lifting the sliver; IPC-2221 external 1 oz 1.0 mm ≈ 2 A at ΔT 10 °C | geometry | Add cut guidance to the bench list |

**Could not verify:** net-tie DRC acceptance (needs a board; Nick's first DRC); Pi Zero 2 W
USB VBUS wiring (needs a primary source); how far VBUS back-feed reaches past L1.

**Repo untouched:** clean before and after, HEAD 658bd7d.

### Design-agent response

| # | Action |
|---|---|
| F1 | Checked a primary source: Raspberry Pi Zero 2 W reduced schematic (RPI-ZERO2W_R1, 2021-10-15): power micro-USB J1 pin 1 → 5V directly (C1 47 µF; no diode/fuse shown); header J8 pins 2/4 on 5V. The data port isn't shown in the reduced schematic, so (a) stays unconfirmed. U10's body-diode path isn't stated in SLUSEF4A but is inherent to its synchronous NMOS high side. Mechanism written into D14 and SPEC; schematic note and bench item now say *any* USB cable. **Nick decided (2026-10-05): procedure only** — bench rule: never plug a USB 5 V source into the Pi on a bridged board, shield powered or not; Pi-powered peripherals are fine. Written into D14, SPEC, the schematic note and the bench list |
| F2 | Fixed: note cites D14 and covers any USB cable (power or data) |
| F3 | Fixed: Demo line has S4.b's numbers and nets; "S4.a converter (done)" |
| F4 | Fixed: footprint renamed `nereus:SolderJumper-2_R1210_Bridged_NetTie` (file, footprint name, Value, schematic field, docs) |
| F5 | Fixed: dead branch removed; lib_pins still returns J1's 40 pins; test passes |
| F6 | Fixed: cut guidance in the footprint description and a new bench item ("score both ends, lift the copper, check open with a meter") |

---

## Round 2 — 2026-10-05 — APPROVED WITH NITS

*Same standing S4 QE session; report sent straight to the design session. Reviewed
`8baa028`. Findings verbatim; claims summarised.*

**Claims checked (summary), all ✅:** check.sh numbers (78/629, 53/53, tests 7/3/12/5);
connectivity identical to round 1 and the base diff unchanged; F1 regex + guard + test
(set_properties with no changes on all 197 symbols: 0 raises, 0 changes); stale fields
gone, C58 10V visible; F8 move is only C58, #PWR75, the junction and 4 wires
251.46 → 254 (off-grid count unchanged); F2–F7 docs; TI Figure 9-1 C_IN 2.2 µF and
Table 9-2 confirmed; viewer in sync; PR body matches.

| # | Severity | Finding | Evidence | Suggested fix |
|---|---|---|---|---|
| N1 | NIT | qe/S4.md F1 says "GRM21BB is 2.0 × 1.25 × 1.25 mm"; "GRM21BB" is an artifact of markdown bold; the prefix is GRM21B | qe/S4.md:31 | "GRM21B (thickness code B) is 2.0 × 1.25 × 1.25 mm" |
| N2 | NIT | C58's "10V" text starts ~0.3 mm from the right end of its GND symbol's top bar; legible, no overlap | render x 250–262, y 220–230 mm; property at (256.54, 228.42) | Optional: move it ~1.27 mm right |
| N3 | NIT | Bench item "5V_PI stays above ~4.8 V under load" leaves ~20 mV margin against the 4.82 V worst-case setpoint; a healthy unit could fail it | viewer bench list; D13 | Judge by droop from the measured no-load value, or by margin above the Pi's undervoltage threshold (cite it) |

**Could not verify:** P890.B independently (accepts the fetch + Nick's byte-identical
download); Murata pages and C56/C57 effective capacitance (open in SPEC).

**Repo untouched:** clean before and after, HEAD 8baa028.

### Design-agent response

| # | Action |
|---|---|
| N1 | Fixed in round 1's text above |
| N2 | C58's 10V field moved 1.27 mm right (257.81, 228.42) |
| N3 | Bench item reworded: droop from the measured no-load value, and margin above the Pi's undervoltage threshold (threshold to be cited in S4.c) |

---

## Round 1 — 2026-10-05 — CHANGES REQUESTED

*Fresh S4 QE session, reviewed `0f5958a` against base `09af9d8`. Verdict and findings
verbatim; the claims table is summarised (full text in the QE session's transcript).*

**Verdict:** CHANGES REQUESTED, 1 MAJOR (set_properties silently skips fields with
escaped quotes, so C56/C57 keep stale 0603 data), plus 2 MINOR and 5 NIT.

**Claims checked (summary), all ✅ except values/fields (⚠️ → F1):** ERC 76/562 →
78/629 with +2 errors exactly U10 Pin 6 (CB) and Pin 2 (SW); +57 off-grid all in the
copy; +10 footprint links = U10, L6, C53–C55, R37–R40, TP38; existing parts'
connections identical; new nets exactly as claimed; pin-for-pin mirror of U5 (C57
the only extra); 60 of 73 new items at exactly +76.2 mm; only placement changes on
the Top-Level sheet; refs above the mote board's max; 0 duplicate uuids, correct
instance paths; netcheck 53/53; midwire 0; tests OK; TI facts confirmed against
SLUSEF4A; Eq. 14 → 21.8 µF; ripple 12.7–15.6 %; hard constraints OK; docs and viewer
consistent. Own checks: Vout 4.82–5.14 V worst case; Ton 142 ns at 32 V (126 ns at
36 V) vs 70 ns min; peak current limit 6.68 A max < Isat 8.4 A; EN ≈ 12.4 V; output
ripple (C term) ≈ 2 mV.

| # | Severity | Finding | Evidence | Suggested fix |
|---|---|---|---|---|
| F1 | MAJOR | `set_properties()` silently skips any property whose value contains an escaped quote, so `keep_only` left stale 0603 data on the new parts C56/C57: `THICKNESS (MAX)` = `0.039\"(1.00mm)` and `SIZE / DIMENSION` = `0.063\"Lx0.031\"W(1.60mmx0.80mm)` (GRM21B, thickness code B, is 2.0 × 1.25 × 1.25 mm; QE round 2 N1 corrected "GRM21BB"). Wrong BOM/height data on a newly sourced part, and the tool failed quietly (value 6) | Power sheet lines 7705, 7763; PROP regex `"([^"]*)"` can't match `\"` | Make PROP's value `"((?:[^"\\]|\\.)*)"`; optionally have `keep_only` raise if any `(property` line wasn't matched; add a test; re-run on C56/C57 and re-verify the netlist |
| F2 | MINOR | U10 carries far more power than U5; RθJA 107.8 °C/W (SLUSEF4A §7.4) → ~45–65 °C rise for ~0.4–0.6 W IC loss before potting derating. SPEC rule 8 not addressed or scheduled; the S4.c item covers bus current only | TRACKER S4.c | Extend S4.c to a U10/L6 loss + thermal estimate at max Pi load (potted), or add to SPEC open questions |
| F3 | MINOR | TRACKER rule 5: the S4 Demo line has no command or expected numbers | TRACKER S4 block | Copy the PR's demo |
| F4 | NIT | D13's "10–13 %" for the 3.3 V converter: nominal 8.2 µH at 16–32 V gives 9.7–10.9 %; basis not stated | ΔiL = 3.3(Vin−3.3)/(Vin·8.2µ·1.1M) | State the basis, e.g. 10–11 % (3V3) vs 13–16 % (5 V) |
| F5 | NIT | TI Table 9-2 (1.1 MHz, 5 V) suggests 3.3 µH (L6 is 2.5×); U5's 8.2 µH is 3.7× TI's 2.2 µH and field-proven; §9.2.2.4: low ripple weakens comparator SNR | SLUSEF4A Table 9-2, §9.2.2.4 | One sentence in D13; add a SW-node jitter check to bring-up |
| F6 | NIT | Vout band not recorded: 4.82–5.14 V worst case | arithmetic | Add to D13/SPEC |
| F7 | NIT | R38's part number has no Yageo citation in SPEC facts | SPEC | Add a citation |
| F8 | NIT | C57's "22µF" text ~0 mm from C58's plate; C58 shows no voltage rating while C56/C57 show 16V | SVG crop x 240–256, y 210–226 | Nudge C58 one grid right or move C57's text; show C58's 10V |

**Could not verify:** Pulse P890.B figures (server refused; L6 = vetted L3, low risk);
Murata product pages (part-number decode matches); C56/C57 effective capacitance at 5 V.

**Repo untouched:** clean before and after, HEAD 0f5958a.

### Design-agent response

| # | Action |
|---|---|
| F1 | Fixed: PROP now accepts escaped characters; `set_properties` raises if any `(property` line in the block didn't parse; new test with an escaped-quote value (12 tests). Re-ran on C56/C57/C58: both stale fields gone (property lists checked). Netlist connectivity and values identical to round 1's head |
| F2 | S4.c item extended (U10/L6 losses + temperature rise at max Pi load, potted); added to SPEC open questions with RθJA cited |
| F3 | S4 Demo line now has the command and expected numbers |
| F4 | D13 now states the basis: 12.7–15.6 % (5 V) vs 9.7–10.9 % (3.3 V), 16–32 V, nominal L |
| F5 | D13 sentence added; bench bring-up list (viewer) has "check U10's SW node for jitter at full and light load". Table 9-2 verified by rendering SLUSEF4A p. 16: it also shows TI's Figure 9-1 uses C_IN = 2.2 µF (recorded in SPEC; softens the input-cap open question) |
| F6 | Vout 4.82–5.14 V in D13 and the viewer |
| F7 | SPEC fact added (Digi-Key listing 311-13.7KLRCT-ND) |
| F8 | C58 + GND moved one grid right (x = 254; rail wires and junction follow); its 10V now shown under 4.7uF. Render checked |
| Could not verify — P890.B | The design agent read P890.B (01/22) via fetch; Nick's download of the same file is byte-identical (SHA-256) |
