nickraymond/nereus_Pi_shield_ADIN2111/docs/design-review/qe/S3.md

# QE reviews — S3 (PR #7)

*Reports from the standing S3 Quality Engineer session, saved by the design agent.
Newest round first. Design-agent responses follow each round.*

---

## Round 2 — 2026-10-05 — APPROVED WITH NITS

*Same standing S3 QE session; report sent straight to the design session. Reviewed
`004fdcf` against base `c693584`. Findings verbatim; claims summarised (full text in
the QE session's transcript).*

**Claims checked (summary), all ✅:** still docs only (`nereus_Pi_shield_ADIN2111`
and `tools` identical to base, so round 1's ERC 76/562 and netcheck 53/53 stand);
F1 README matches SPEC and D12; F2 Q1 deferred and consistent across
SOFAR_QUESTIONS, viewer, Icebox and Later; F3, F4, F5 fixed; viewer parses (JXA,
15 sections) and matches TRACKER; no stale 50 W / 2.083 for this board; process
change consistent in TRACKER rule 3.4 and quality-engineer.md; qe/S3.md records
round 1 faithfully.

| # | Severity | Finding | Evidence | Suggested fix |
|---|---|---|---|---|
| 1 | MINOR | The PR description is now stale. It says Q1 is unchanged and doesn't list the round-2 files or the process change | `gh pr view 7` body: "Q5 → `[-]` deferred (new state key); Q1–Q4 unchanged". No rows for README.md, .claude/agents/quality-engineer.md, docs/design-review/qe/S3.md, and nothing on TRACKER rule 3.4 | Update the body |
| 2 | MINOR | The process change isn't fully wired in. (a) The QE role file's frontmatter is `tools: Read, Grep, Glob, Bash`, with no session-message tool. (b) PROMPTS.md §5 still says "When it finishes, save its report…" and doesn't make the request name the design session id | quality-engineer.md:4; PROMPTS.md:51-56 | (a) Add SendMessage to `tools:`, or say the QE runs as a normal Code session whose session-message tool is available. (b) Update §5 |
| 3 | NIT | DEV_LOG S3 entry: round-1 bullets sit under "Broke/surprised us"; Files touched incomplete; Next out of date | docs/DEV_LOG.md:24-43 | Move bullets, extend Files touched, update Next |
| 4 | NIT | The TRACKER S3 demo line lists README but not `.claude/agents/quality-engineer.md` | `git diff --stat c693584 HEAD` | Add "the QE role file" |
| 5 | NIT | qe/S3.md says the findings table is kept "verbatim", but parts are condensed | qe/S3.md:10-12 | Say "condensed" |

**Could not verify:** the viewer in a browser (no Node; JXA parse only); whether a
QE started from the agent definition gets SendMessage when `tools:` is enforced
(depends on how the session is launched).

**Repo untouched:** `git status --short` before and after: empty.

### Design-agent response

| # | Action |
|---|---|
| 1 | PR body updated: Q1 and Q5 deferred, Q3 reworded; README, quality-engineer.md, PROMPTS and qe/S3.md listed; process change noted |
| 2 | (a) Second option: the paragraph now says the QE runs as a normal Code session, so the session-message tool is available; the `tools:` list applies only to sub-agent use, which is forbidden. I didn't widen the frontmatter tool list. (b) PROMPTS §5 now has the request carry the design session id; later rounds go to the same session |
| 3 | Fixed |
| 4 | Fixed: "…CLAUDE.md, the skill and the QE role file" |
| 5 | Fixed: round 1 header now says condensed |

---

## Round 1 — 2026-10-05 — CHANGES REQUESTED

*Fresh S3 QE session, reviewed `21ff25d` against base `c693584`. Condensed: verdict,
findings, could-not-verify and claims all shortened (finding 2 and several
suggested fixes included); the full text is in the QE session's transcript.*

**Verdict:** CHANGES REQUESTED. The schematic side checks out completely: the
netlist is identical to the base and every count matches the claims. Two
consistency misses contradict D12 (the README headline; Sofar Q1 still marked
"send when ready" with 50 W wording).

**Claims checked (summary), all ✅:** no change under `nereus_Pi_shield_ADIN2111/`,
`KiCAD_reference_designs/`, `Archive/`, no `.kicad_pcb`; ERC 76/562 (base also
76/562; label_dangling 18, pin_not_connected 41, power_pin_not_driven 8,
unresolved_variable 9); netcheck 53/53, 0 opens, 0 shorts, 0 excluded; netlist
pin-to-net groupings identical to the base (111 nets, 111 parts; raw diff only the
library `uri`); L1/L2 SRF1260-101M and every SPEC-constraint-7 part unchanged;
890 mA / ~20 W consistent with SPEC's fact and POWER_PATH §1; tests OK ×4,
midwire 0; TRACKER and viewer agree (S3 3 items, flags [x][x][ ]); viewer script
parses (JXA, 15 sections); D7/D8/D12, SPEC, banner, Q5, CLAUDE.md, /agent-entry,
DEV_LOG and changelog consistent.

| # | Severity | Finding | Evidence | Suggested fix |
|---|---|---|---|---|
| 1 | MAJOR | The README, the repo's front page, still states the old goal: a 50 W board. It contradicts D12 and SPEC's new goal | `README.md:5`: "a 24 V payload port, and a ~50 W power path (absolute max at 24 V). Potted." This file is not in the diff | Make it match SPEC's goal |
| 2 | MAJOR | Sofar Q1 (the e-fuse question) still asks about a 50 W design and is marked "send when ready", while the same PR moves the e-fuse work and Q1 into the deferred 50 W work | `SOFAR_QUESTIONS.md:12` Q1 `[ ]` "What do you recommend for a ~50 W potted design?"; TRACKER Icebox and viewer Later list Q1 as deferred; viewer intro says "Send Q1–Q4 when ready" | (a) Defer Q1 like Q5 (consistent with SPEC constraint 7), or (b) reword it for this board and drop it from the Icebox/Later lists |
| 3 | MINOR | Q3's "why" column still compares against ~50 W; Q3 is still live | `SOFAR_QUESTIONS.md:14` "Payload port rating vs ~50 W" | "Payload port rating vs the mote's 890 mA (D12)" |
| 4 | NIT | Inside the deferred POWER_PATH, two lines still frame the study as the current sprint | `POWER_PATH.md:3` "Working trade study for Sprint S3"; `:58` "same basis in S3" | Optional rewording |
| 5 | NIT | TRACKER's S3 demo line says the diff "touches docs only"; it also touches CLAUDE.md, the skill and the viewer | TRACKER S3 demo line vs `git diff --stat` | Copy the PR's wording |

**Could not verify:** that *More Power Delivery* says exactly 890 mA (taken from
SPEC's existing confirmed fact; agrees with SRF1260 Irms 0.892 A); that Nick made
the decision on 2026-10-05 (conversation outside the repo); the viewer in a
browser (no Node; script parse checked under JXA).

**Repo untouched:** `git status --short` before and after: empty.

### Design-agent response

| # | Action |
|---|---|
| 1 | Fixed: README now says the mote's power path unchanged (~20 W, 890 mA; 50 W in a later revision) |
| 2 | Option (a): Q1 → `[-]` deferred with the 50 W revision (no protection added on this board, D12); viewer intro "Send Q2–Q4", viewer Q1 marked deferred. Nick can reverse this |
| 3 | Fixed as suggested |
| 4 | Fixed: "started in Sprint S3 and deferred to the 50 W revision (D12)"; "in the 50 W revision" |
| 5 | Fixed: "touches only docs, the viewer, README, CLAUDE.md and the skill" |
| Viewer in a browser | Checked by the design agent before the PR: renders, 26 of 86 done |
| Process | From now on the QE sends its report straight to the design session (TRACKER rule 3.4, `quality-engineer.md`) |
