nickraymond/nereus_Pi_shield_ADIN2111/docs/design-review/qe/S2.md

# QE reviews — S2 (PR #5)

*Reports from independent Quality Engineer sessions, saved by the design agent.
Rounds 1 and 3 are verbatim; round 2 is condensed (its findings table verbatim,
claims summarised; the full text is in the QE session's transcript). Newest round
first. Design-agent responses follow each round.*

---

## Round 3 — 2026-10-05 — APPROVED

*Same standing QE session as round 2 (one standing QE per sprint), reviewed `328b4be`. Saved verbatim.*

# QE review — PR #5 (S2) — round 3 — 2026-10-05
**Verdict:** APPROVED — all N1–N7 fixed, no regressions; two NITs below are non-blocking. Nick's KiCad review can proceed.
**Reviewed:** `328b4beefcb2` (one commit on top of `f2eb36f`), base `07fb984` — `tools/ercsum.py`, `tools/test_ercsum.py`, DESIGN, TRACKER, checklist, DEV_LOG, `qe/S2.md`, `quality-engineer.md`, PR body.

Pre-flight: `$PR` HEAD = `origin/sprint/2-pi-header` = `headRefOid` = `328b4bee…`, `$PR` clean, base `07fb984`. `git diff --quiet f2eb36f 328b4be -- nereus_Pi_shield_ADIN2111` → no change (no `.kicad_sch`/project file touched).

## Round-2 findings
| # | Fixed? | Evidence |
|---|---|---|
| N1 | ✅ | DESIGN:96, TRACKER S5, checklist now say "unconnected on the Top-Level sheet since import"; verified against mote copper (SW_PGOOD = U9.2, R33.1, TP34.1; SW_FLAGB = U9.7, R35.1, TP35.1) and our netlist (SW_FLAGB={R35.1,TP35.1,U9.7}, SW_PGOOD={R33.1,TP34.1,U9.2}) — your U9 pin numbers are correct |
| N2 | ✅ | TRACKER demo + checklist checkpoint: "−27/+38 vs S1; 30 are J1 pins" — matches ERC (29 J1 pin_not_connected + 1 J1.2 power_pin_not_driven) |
| N3 | ✅ | DESIGN pin_not_connected row: "pin 2 (5V, stacked with 4)"; `ercsum` lists J1 pin 2 in both types |
| N4 | ✅ | Totals line removed → `ercsum: no 'ERC messages … totals line'`, exit 1; item kind dropped → "counts don't match", exit 1; `--items` prints `29 × J1 pins (2, 3, 5, …, 40)` and `1 × J1 pins (2)`; `test_ercsum`: 5 tests OK |
| N5 | ✅ | `test_ercsum.py` in TRACKER:56, agent-file Tests bullet, PR body Tests line |
| N6 | ✅ | "the PoDL and Power Monitor sheets' SCL/SDA" |
| N7 | ✅ | S5 duplicates removed (27/28 only under "avoided"; SW_FLAGB/SW_PGOOD merged into the 36/38/40 item); checklist mirrors; agent-file `git archive $B` + groupings sentence back under the connectivity bullet |

## Claims checked (regression at `328b4be`)
| Claim | Result | Evidence (command → output) |
|---|---|---|
| ERC | ✅ | Fresh `kicad-cli sch erc` on `git archive 328b4be` → `ercsum --items`: 41/18/8/9 = 76, 428/111/12/11 = 562, `(report: 76/562)`, exit 0 — identical to round 2 |
| Connectivity vs base | ✅ | 277 common-part pins, 0 grouping changes, 0 name changes; removed P1, R9, 12 TPs; added J1 |
| netcheck / midwire | ✅ | `53/53 copper nets matched; 0 opens, 0 shorts, 0+0 unpaired pins; 0 parts excluded`; `midwire: 0 pin location(s) mid-wire` |
| Tests | ✅ | test_netcheck / test_midwire / test_schedit / test_ercsum all OK |
| Hard constraints | ✅ | `diff --name-status 07fb984...328b4be`: no `.kicad_pcb`, `Archive/`, `KiCAD_reference_designs/` paths |
| Docs consistency | ✅ | TRACKER, checklist (JS parses), DESIGN, DEV_LOG, PR body agree on 76/562, −27/+38, round-2/round-3 status; "one standing QE session per sprint" consistent across D10, TRACKER nibble 4, agent file |

## Findings
| # | Severity | Finding | Evidence | Suggested fix |
|---|---|---|---|---|
| R1 | NIT | `qe/S2.md` header says reports are "saved verbatim", but the round-2 section is a condensed rendering (findings table complete, claims tables summarised) | `qe/S2.md`:3–4 vs round-2 section | Either save verbatim or change the header to "verbatim or condensed (findings tables verbatim)" |
| R2 | NIT | TRACKER header still "Last updated: 2026-10-04" | TRACKER:4 | Bump to 2026-10-05 |

## Could not verify
- KiCad GUI appearance (Nick's step).

## Repo untouched
git status before: `$PR` clean (`328b4be`); QE worktree clean / after: `$PR` clean (`328b4be`); QE worktree clean. All outputs in scratchpad; no state-changing git/gh commands.

### Design-agent response to round 3 (2026-10-05)
R1: header now says rounds 1 and 3 are verbatim and round 2 is condensed (findings table verbatim). R2: TRACKER date bumped. Docs-only; no further QE round needed per the QE's verdict.

---

## Round 2 — 2026-10-05 — APPROVED WITH NITS

*QE session: "QE review round 2: PR #5 (S2)" (fresh session), reviewed `f2eb36f` against base `07fb984`.*

**Verdict:** APPROVED WITH NITS — schematic correct; F1–F5 fixed, F6 mostly fixed; two MINOR doc
errors remain (text-only).

**Round-1 findings:** F1 ✅ (leftovers N2, N3) · F2 ✅ · F3 ✅ (single hunk: MEZZANINE text_box
removed; no mezzanine text left in any sheet) · F4 ✅ · F5 ✅ · F6 ⚠️ partly (decision order fixed;
pin_not_connected row still said "pin 4" — N3).

**Claims re-verified independently:** kept connectivity identical (277 common-part pins, 0
grouping/name changes); J1 GND 8/8; J1.1/J1.17 on no net + NC at (127, 55.88), 3V3 net has no
J1 pin; J1.2/J1.4 own net; J1/#PWR66/#PWR67/#FLG01/#FLG02 unique, 0 duplicate UUIDs; netcheck
53/53, 0 opens/shorts/excluded (body identical to committed); midwire 0; ERC 76/562 with
41/18/8/9 and 428/111/12/11, ercsum exit 0; ercsum fails loudly on a dropped item kind; all 4
test files pass; no `.kicad_pcb`/Archive/reference-design changes; checklist in sync.

| # | Severity | Finding | Evidence | Suggested fix |
|---|---|---|---|---|
| N1 | MINOR | The F1 fix introduced an unverified fact: SW_FLAGB/SW_PGOOD's "partner was P1" / "dangling since P1 went". On the mote these nets never reached P1; the sheet pins were already unconnected before S2 (engineering value 3) | Mote copper: SW_FLAGB/SW_PGOOD pads are only U9, R33/R35, TP34/TP35; base ERC at `07fb984` already lists both sheet pins | Reword: "unconnected on the Top-Level sheet since import (on the mote they go only to U9/R33/R35/TP34/TP35)" |
| N2 | MINOR | TRACKER S2 demo still said "the 29 extra errors are J1 pins"; checklist "ERC 76, of which 29 are J1 pins". Errors rose by 11; J1 accounts for 30 (29 + J1.2) | `git diff 15e01e3 f2eb36f -- docs/TRACKER.md` doesn't touch line 117 | "(−27/+38 vs S1; 30 are J1 pins for S4/S5)", same in checklist |
| N3 | NIT | DESIGN pin_not_connected row says "pin 4 (5V, stacked with 2)"; ERC reports J1 Pin 2 there too | All ERC runs list `Symbol J1 Pin 2 [5V, Power input]` at (116.84, 55.88) in both types | "pin 2 (5V, stacked with 4)" |
| N4 | NIT | ercsum: missing totals line → cross-check silently off, exit 0; no test of `main()`/mismatch path; J1 collapsed to "J1 pins" hides pin numbers (how N3 slipped) | totals line stripped → exit 0 | Missing totals → exit 1; add mismatch test; keep pin numbers |
| N5 | NIT | `test_ercsum.py` missing from test commands (TRACKER, PR body, agent file) | TRACKER:54 etc. | Add it |
| N6 | NIT | DESIGN says "the Power Monitor sheet's SCL/SDA"; one pair is on the PoDL sheet | PoDL.kicad_sch:4800/4899, PowerMon.kicad_sch:1180/1191 | "the PoDL and Power Monitor sheets' SCL/SDA" |
| N7 | NIT | TRACKER S5 duplicates (SW_FLAGB/SW_PGOOD → 38/40 twice; 27/28 twice; checklist doesn't mirror one); agent-file "Compare pin-to-net groupings…" sentence under the wrong bullet | TRACKER S5:157/167, :152–153/166 | De-duplicate, move the sentence |

**Note for Nick:** on the mote SW_FLAGB/SW_PGOOD have R33/R35 pull-ups and TP34/TP35 test points;
S5's wiring to Pi pins 38/40 can reuse them.

**Could not verify:** KiCad GUI appearance (Nick's step). **Repo untouched:** `$PR` clean (`f2eb36f`)
before and after; QE worktree clean; outputs in scratchpad only.

### Design-agent response to round 2 (2026-10-05)

| # | Fix |
|---|---|
| N1 | Confirmed in copper (SW_PGOOD = R33.1, TP34.1, U9.2; SW_FLAGB = R35.1, TP35.1, U9.7). Reworded in DESIGN, TRACKER S5 and the checklist; S5 now reuses R33/R35 and TP34/TP35. I stated it without checking — lesson recorded in DEV_LOG |
| N2 | TRACKER demo and checklist: "−27/+38 vs S1; 30 are J1 pins for S4/S5" |
| N3 | "pin 2 (5V, stacked with 4)" |
| N4 | ercsum: missing totals line → exit 1; J1 line lists pin numbers; 3 new tests (main OK, mismatch, missing totals) |
| N5 | `test_ercsum.py` added to TRACKER, agent file and PR body |
| N6 | "the PoDL and Power Monitor sheets' SCL/SDA" |
| N7 | S5 duplicates merged (27/28 kept once under "avoided"); agent-file sentence moved under the connectivity bullet |
| Process | One standing QE session per sprint (Nick, 2026-10-05): TRACKER nibble 4, agent file, D10 |

---

## Round 1 — 2026-10-05 — CHANGES REQUESTED

*QE session: "QE review: PR #5 (S2 mezzanine → Pi header)", reviewed `15e01e3`.*

# QE review — PR #5 (S2) — 2026-10-05
**Verdict:** CHANGES REQUESTED (schematic work is correct; one MAJOR documentation-accuracy finding on ERC error accounting — fix is docs-only)
**Reviewed:** commit `15e01e322df4` — `BM_Mote_1_Master.kicad_sch` (only schematic file changed), docs listed in claim 10, `pi-shield-checklist.html`, `tools/schedit.py` + tests, process commits `6db6c73`/`15e01e3`. Baseline = `origin/main` = `07fb984` (= PR `baseRefOid`); local `main` in this clone is stale (`df9a3de`) so was not used — see F4.

## Claims checked
| Claim | Result | Evidence (command → output) |
|---|---|---|
| PR head | ✅ | `rev-parse HEAD` = `origin/sprint/2-pi-header` = `gh pr view 5 headRefOid` = `15e01e322df4…`; status clean |
| 1. Deletions | ✅ | Master sheet parsed both sides: symbols removed = `#PWR04/07/11/12/13, P1(×2 units), R9, TP4/6/9/10/11/12/14/15/16/17/18/33`; labels removed = exactly the 14 listed; NCs removed (110.49,149.86),(110.49,154.94); wires 128→64 (69 removed, 5 added incl. 2 trimmed I2C1 stubs); junctions 24→13 (12 removed, 1 added) |
| 2. Kept | ✅ | R10, TP19 present (SW_ON={R10.1,R32.1,U9.4}; R10.2↔TP19); `I2C1_SDA/SCL` labels at (162.423,127)/(162.829,129.54) still name nets with U4.5/6; all 7 `ADIN_*` labels present; VBUS_OUT={C50,D3,R11.2,TP36,U9.8} |
| 3. Kept connectivity | ✅ | Netlist diff before/after: 277 pins on common parts, **0** pins with changed grouping, **0** with changed net name; nets gone = 14 mezzanine + `unconnected-(P1/TPx)`; new = only J1 nets |
| 4. J1 placement | ✅ | (121.92, 88.9), footprint as stated (exists in KiCad lib); `lib_symbols` entry s-expr-identical to stock `Connector.kicad_sym:Raspberry_Pi_2_3` (PWR_FLAG also identical to stock `power.kicad_sym`) |
| 5. J1 connections | ✅ | GND ⊇ J1.6/9/14/20/25/30/34/39 (8/8); `unconnected-(J1-3V3-Pad1)`={1,17} only, NC at (127,55.88); `Net-(J1-5V-Pad2)`={2,4}; J1/#PWR66/#PWR67/#FLG01/#FLG02 each unique across all sheets; paths `/30e82bf5…/3c398828…` (= R10's); no duplicate UUIDs in project |
| 6a. netcheck | ✅ | `netcheck: 53/53 copper nets matched; 0 opens, 0 shorts, 0+0 unpaired pins; 0 parts excluded` — report body identical to committed `netcheck.md` |
| 6b. midwire | ✅ | `midwire: 0 pin location(s) mid-wire` |
| 6c. ERC totals | ✅ | `Errors 76  Warnings 562` (identical to design agent's `out/erc.rpt`) |
| 6d. ERC breakdown | ❌ | Actual errors: pin_not_connected **41**, label_dangling 18, power_pin_not_driven 8, unresolved_variable 9 (claim says 33 → sums to 68, not 76) — see F1. Warnings 428/111/12/11 ✅ |
| 7. Tests | ✅ | test_netcheck 7 OK, test_midwire 3 OK, test_schedit 7 OK |
| 8. Visual | ✅ (1 stale text — F3) | SVG→PNG render: J1 in clear space, GND/PWR_FLAG/junction/VBUS flag tidy; no orphan wires/labels (all 11 `unconnected_wire_endpoint` pre-exist on main) |
| 9. Hard constraints | ✅ | `diff --name-status origin/main...HEAD`: no `.kicad_pcb`, `Archive/`, or `KiCAD_reference_designs/` paths; Pi 3V3 not tied to shield 3V3 (3V3 net 18→15 nodes, P1.2/4/6 removed, no J1 pins) |
| 10. Docs consistency | ⚠️ | TRACKER S2, checklist (JS parses; S2 items), changelog agree; DESIGN ERC owner table + warnings paragraph wrong (F1, F2); DEV_LOG/PR text stale on I2C pull-ups (F5) |
| 11. Process commits | ✅ (nits) | D10/D11, TRACKER nibbles 3–6, PROMPTS #5, CLAUDE.md, S5 pull-up task consistent; SPEC open question added in `ec28d44` removed in `6db6c73` (resolved by D11). Nits F4, F6 |

## Findings
| # | Severity | Finding | Evidence | Suggested fix |
|---|---|---|---|---|
| F1 | **MAJOR** | DESIGN.md "Remaining ERC errors after S2 (76)" table is wrong, so the PR claim "Every remaining error has an owner in DESIGN.md" is false. pin_not_connected is 41 not 33; 9 errors have no owner: FID1–6 hidden NC pins (6), Load Switch sheet pins SW_FLAGB & SW_PGOOD (2), and `#PWR34` ADIN_VDDIO in power_pin_not_driven (1). The table's rows sum to 68, not 76. The PR's "−18 mezzanine / +29 J1" delta is also wrong: actual −27 (12 TPs, 13 mezzanine labels, U5 VIN, U6 GND) / +38 (29 J1 pins, 8 newly-dangling I2C1/SDA/SCL labels, J1.2 power pin). (The FID + sheet-pin miss was already in S1's table, which said 16 vs actual 24.) | `erc_pr.rpt` pin_not_connected list: 29×J1, `Hierarchical Sheet Pin SW_FLAGB/SW_PGOOD`, `FID1..6 Hidden pin 0`, MTG1–4; power_pin_not_driven includes `Symbol #PWR34 Hidden pin [ADIN_VDDIO]` | Correct the table: pin_not_connected 41 (J1 29 → S4/S5; SW_FLAGB/SW_PGOOD → S5; FID1–6 → S6 justify/exclude; MTG1–4 → Nick); add #PWR34 to power_pin_not_driven; correct the −/+ decomposition in DESIGN results row, changelog, DEV_LOG, TRACKER demo text and PR description |
| F2 | MINOR | DESIGN.md warnings paragraph still states S1 numbers | Line 101: "Warnings (590)… 426 off-grid… 126 footprint… 26 dangling" vs actual 562 = 428+111+11+12 | Update (the +2 off-grid come from trimmed I2C1 wires ending on off-grid Altium label anchors 162.423/162.829) |
| F3 | MINOR | A stale "MEZZANINE" text box sits directly under J1 on the Top-Level sheet — mezzanine leftover inside S2.1 scope; also a stale "Processor + onboard logic runs off 3V3" note | `text_box "MEZZANINE"` at Master sheet line 6274; visible in render below J1 | Delete or rename "RASPBERRY PI HEADER"; log the processor note for S6 |
| F4 | MINOR (process) | `quality-engineer.md` (and this review prompt) say `git archive main`; in this clone local `main` = `df9a3de` (pre-S0), not the PR base `07fb984`. Literal use diffs against the wrong baseline (`diff --stat main...HEAD` shows 97 files incl. Archive/reference-design deletions) | `git rev-parse main origin/main` → `df9a3de…` / `07fb984…` | Use `origin/main` (or `gh pr view N --json baseRefOid`) in the agent file |
| F5 | NIT | PR "Found along the way" says "confirm the Pi's GPIO2/3 pull-ups… or add them" and DEV_LOG says "Logged for S5 (SPEC open question)" — both superseded by D11 (decision to add) and the SPEC question's removal | `git show 6db6c73 -- docs/SPEC.md` (3 lines removed) | Point both at D11 |
| F6 | NIT | Decision log out of order (D8, D10, D11, D9); ERC owner table says "pin 4 (5V)" — ERC reports J1 **Pin 2** (stacked 2/4) | DESIGN.md lines 74–79 | Reorder; say "pin 2 (5V, stacked with 4)" |

**Risks for later sprints (no action in S2):**
- **S5 / D11 pull-ups:** the Pi has its own pull-ups on GPIO2/3 (Raspberry Pi documentation states 1.8 kΩ fixed — cite a primary source in S5); 4.7 kΩ in parallel → ≈1.3 kΩ. The pull-ups go to the *shield's* 3V3 while the Pi has a separate 3V3 rail: if one rail is up and the other down, current can back-power through pull-ups/IO clamp diodes (same applies to the ADIN SPI/control lines). S5 should choose the pull-up rail and document power sequencing.
- **Layout (Nick):** the 2×20 socket mates from the shield's underside → J1 goes on B.Cu; check pin-1 orientation against the Pi.
- **S5 pin choice:** keep pins 27/28 (ID_SD/ID_SC, HAT EEPROM) unassigned unless HAT ID is implemented.
- **VBUS_OUT** previously fed P1 pins 14/16/18 (payload power); it now has no external outlet until S5's 2-pin connector.

## Could not verify
- KiCad GUI appearance (SVG renders converted with Quick Look only; that is Nick's step).
- ERC/netlist were run on `git archive` copies (no ignored `fp-info-cache`/`.kicad_prl`); counts matched the design agent's `out/erc.rpt` exactly, so treated as equivalent.

## Repo untouched
- `$PR` (`git -C $PR status --short`): before (empty/clean) / after (empty/clean)
- QE worktree: before (empty/clean) / after (empty/clean)
- All outputs in scratchpad `qe.jASF/`; no state-changing git or gh commands run.

### Design-agent response to round 1 (2026-10-05)

| # | Fix |
|---|---|
| F1 | Confirmed (my hand filter matched `Symbol … Pin` and missed `Hidden pin` / `Hierarchical Sheet Pin`). DESIGN ERC owner table corrected: pin_not_connected 41 (J1 29 → S4/S5; SW_FLAGB/SW_PGOOD → S5; FID1–6 → S6; MTG1–4 → Nick), #PWR34 added to power_pin_not_driven. −27/+38 decomposition corrected in DESIGN results row, changelog, DEV_LOG and the PR description. Root cause: new `tools/ercsum.py` (+ test) builds these tables and checks they sum to the report totals |
| F2 | DESIGN warnings paragraph updated to 562 = 428 + 111 + 11 + 12 (+2 off-grid explained) |
| F3 | `MEZZANINE` text box deleted (netlist and ERC unchanged). Processor note logged as an S6 item |
| F4 | `quality-engineer.md` now uses the PR's `baseRefOid`, not local `main`, and runs `ercsum` |
| F5 | DEV_LOG and the PR description now point to D11 |
| F6 | Decision log reordered D1–D11; "pin 2 (5V, stacked with 4)" |
| Risks | Added to TRACKER S5: pull-up rail + power sequencing / back-powering; pins 27/28 unassigned; SW_FLAGB/SW_PGOOD → Pi 38/40; combined pull-up value with citation. Layout note (J1 on B.Cu, pin 1) is already in Nick's board checklist |
