nickraymond/nereus_Pi_shield_ADIN2111/docs/SOFAR_QUESTIONS.md

# SOFAR_QUESTIONS.md — Open Questions for Sofar

*Questions about the Sofar mote design that only Sofar can answer. Nick sends
them; record the answer, date and who answered, then move the fact into
SPEC.md or POWER_PATH.md with "Sofar, <name>, <date>" as its source.*
*Last updated: 2026-10-07*

State key: `[ ]` not sent · `[>]` sent, waiting · `[x]` answered · `[-]` deferred (don't send yet)

| # | State | Question | Why we're asking | Answer (who, date) |
|---|---|---|---|---|
| Q1 | [-] | Is there a fuse or e-fuse on the mote's through-power path in any revision? Our 000639-AB copy has none, and you say the mote has no through-current protection. Your 50W/100W guide mentions a Bel C1F2 2 A fuse as a "placeholder". What do you recommend for a ~50 W potted design? | Nick remembered a fuse. The 50 W path needs protection that works in both directions and is safe to pot (POWER_PATH P4). **Deferred with the 50 W revision** (DESIGN D12, 2026-10-05): this board keeps the mote's path, with no protection added | |
| Q2 | [ ] | Is R11 (0 Ω, 1210, across the U9 load switch) fitted on production motes? | Fitted means the payload port is always on. Our copy of the files has it fitted; Nick decided R11 DNP on the shield (D17), so this is now context only | |
| Q3 | [x] | What current limit does R34 (374 kΩ) set on the FPF2700 (U9)? | Payload port rating vs the mote's 890 mA (D12); we couldn't get the datasheet | **Answered from the datasheet, no need to ask Sofar:** ≈ 0.74 A typical, 0.59–0.89 A (Fairchild FPF2700 Rev. 1.0.3, Eq. 1; supplied by Nick, 2026-10-05) |
| Q4 | [-] | Why is the load switch controlled from the mezzanine side? | Deferred (context only): the Pi (GPIO16) is the only controller; the R9/R10 option links are removed (DESIGN D22) | |
| Q5 | [-] | Has MSD1514-473MED (one per port) been built or tested since the guide was written? Any recommended damping values (R15/R16, C22/C23) to go with it? | The guide says it's not qualified at 50 W and that damping should be retuned for new magnetics. **Deferred with the 50 W revision** (DESIGN D12, 2026-10-05) | |
| Q6 | [ ] | May we give each threaded insert's ring pad (MP1–MP4, Würth 78614015360) the bus net in our footprint? On 000639-AB the pad has no net; the bus reaches it from the top-side C-shaped arc (1.2 mm wide, r 3.03 mm, ≈ 290°) through seven 0.6 mm vias on r 3.0 mm into the bottom ring pad. Anything else about the contact to keep (the arc's gap, the via count, the lug on the top arc)? | A netted pad lets our checks see the connection; we copy the contact exactly (DESIGN D24, D31). Reworded 2026-10-07 after measuring the vias (the earlier wording assumed no vias) | |
| Q7 | [ ] | D1 (bus TVS) is listed as ST SMA6F33A with Vishay SMA6F33A-M3/H and ST SMA6F33AY as second sources. Digi-Key shows the ST SMA6F33A as obsolete (2026-10-06). Which source do production motes use now, and is the Vishay part your preferred replacement? | Lifecycle check before our first build (`docs/design-review/bom_lifecycle.md`); we'd rather use your approved source than pick one | |
| Q8 | [ ] | The mote files carry "licensed under a Creative Commons Attribution-NoDerivatives 4.0 International License". Our Pi shield is derived from 000639-AB (PoDL front end, ADIN2111, power path, Altium-to-KiCad copy). How may we share the shield's schematic and board files: with our fab house (JLC) for manufacture, internally, publicly? Do you need to approve it, and what licence and attribution text should the shield's cover page carry? | BY-ND generally doesn't allow sharing adapted material; we keep your notice and say "Derived from Sofar Bristlemouth mote 000639-AB" on every sheet. Raised by the QE in S6.g review; Nick to send. Not legal advice | |
| Q9 | [ ] | Are R12, R13, R17 and R19 (0 Ω 1210) fitted on production motes? Each sits across one winding of its PoDL inductor (R12 across L1 pins 1–3, VBUS–BM1_P; R13 across 2–4, BM1_N–GND; R17/R19 the same on L2); all four are fitted in the 000639-AB files | Fitted, they would tie the data pair to the rails (Bourns SRF1260 windings 1–3 and 2–4), so we suspect DNP in production; we'll match what Sofar builds. Layout question page, 2026-10-07 | |
| Q10 | [ ] | What are the two slots in the ground plane (L3) for, and should a new layout keep them? A slot runs past each PoDL inductor and stops ≈ 27 mm down, so the ground under L1/L2 joins the rest only along the bottom edge. Also: are the two unconnected islands in the power plane (L5) near the upper ears intentional (copper balance?) | Copy deliberate choices, drop accidental ones (D31 copies them as drawn until answered) | |
| Q11 | [ ] | What stackup and fab is 000639-AB built with (copper weights, dielectric thicknesses, impedance target, if any)? The file records only 6 layers and 1.6 mm | Reusing the inner-layer routing unchanged needs the same or an equivalent stackup | |
| Q12 | [ ] | Which layout rules must hold if we move a block as a rigid group: ADIN data pair length or spacing (8–9.5 mm to T1, 18–21 mm to T2 today), distance from the 3V3 buck, bus-to-logic clearance (1–2 mm bus copper, 0.35 mm pour clearance today), and any extra rules for a potted board? | The shield moves whole blocks to fit a Pi Zero outline (D31) | |
