nickraymond/nereus_Pi_shield_ADIN2111/docs/design-review/excluded_parts.txt

# Parts netcheck treats as already removed. One reference per line; text after
# '#' is the reason. Remove each line when the part is actually deleted.
# (Empty since S2: P1, R9 and the 12 mezzanine test points were deleted.)
