nickraymond/nereus_Pi_shield_ADIN2111/experiments/fable_layout_01a/KICKOFF.md

# Kickoff prompt — layout experiment 1.a

Start a new Claude Code session on this repo with **Fable 5.1, high effort**, then paste:

```
Layout experiment 1.a. Read CLAUDE.md, then experiments/fable_layout_01a/BRIEF.md in full; it is your spec and its
hard rules override anything else you infer. Check out the branch experiment/fable-layout-01a (it exists on origin,
created from experiment/fable-layout-01) and work only inside experiments/fable_layout_01a/. KiCad is closed; use
KiCad 9's bundled Python (pcbnew) and kicad-cli. Read experiment 01's REPORT.md, LOG.md and qe/ reports first. Run
milestones M0-M4 autonomously, committing after each with renders in out/ and an entry in LOG.md; I will not answer
questions mid-run, so write OPTIONS.md, decide, and continue. The DFM sweep (M3) takes every JLCPCB limit from
their published pages, cited, never from memory. Stop and write REPORT.md if a hard rule would break or the board
must grow beyond the brief. Never merge; open a draft PR titled "EXPERIMENT (do not merge): fable layout 1.a", then
spawn the Quality Engineer review of that PR as a separate session (docs/PROMPTS.md section 5), save each report in
experiments/fable_layout_01a/qe/, fix and resend until it approves, and tell me the verdict, the PR link and the
pass/fail table.
```

Review afterwards: `OPTIONS.md`, `DFM.md`, `REPORT.md`, the renders in `out/`, the draft PR and the QE reports in `qe/`.

## Session 2 — pick up after QE round 1 (2026-10-08)

The first session ran M0–M2 and stopped on Nick's instruction; QE round 1 of PR #31 is CHANGES REQUESTED. Start a new
Claude Code session (Fable 5.1, high effort) and paste:

```
Layout experiment 1.a, session 2. Read CLAUDE.md, then experiments/fable_layout_01a/BRIEF.md in full (your spec; its
hard rules override anything else), OPTIONS.md, REPORT.md, LOG.md, HANDOFF.md and qe/S7b_01a_round1.md. Check out the
branch experiment/fable-layout-01a (origin, last commit 293dc11; never merge it; PR #31 is the draft PR, base
experiment/fable-layout-01) and work only inside experiments/fable_layout_01a/. KiCad is closed; use KiCad 9's bundled
Python (pcbnew) and kicad-cli; the pipeline is tools/build_all.sh (first run from m0 on a fresh checkout; START=m4
reruns the routing from the M3 snapshot). Never run a milestone script on a board left by a later step.

Finish M2 to the brief's bar, in this order, committing after each with renders in out/ and a LOG.md entry:
1. QE F1 (MAJOR): both ADIN pairs are shorted P-N at the transformer pads (the pair emitter's last segment runs
   through the opposite leg's pad: BM1_DATA_P through T1 pad 2, BM2_DATA_N through T2 pad 1), and
   tools/drcexclude.py's T1/T2 patterns hid them as "Sofar's transformer footprint". Fix the final pad approach in
   router.commit_pair (add the real-board case to tools/test_pair.py first), tighten the exclusion patterns to the
   no-net pads only, and correct REPORT.md: the true split at 293dc11 is 111 Sofar-copied errors + 16 of new copper.
2. QE F2 (MINOR): the ADIN copy region's west clip (mote y 107.9) dropped Sofar's ~{ADIN_INT} via at mote
   (156.571, 107.509), so the pre-route trim removed INT's fan-out (14 items). Keep that connection (re-add the via
   by hand inside the board, or route INT from U1.39 to R1.1 as Sofar did), make tools/dangling.py refuse to trim
   items on a mote pad-to-pad path, and correct REPORT §6 #3's cause.
3. The rest of REPORT.md §6 / HANDOFF.md: the port-1 swap figure colliding with itself (11 DRC errors, BM1_DATA_P
   10.7 mm > 9.5), the VBUS link at U11 pin 1, the two 5V_PI pours, the 3V3 via vs R21 pad 2, VBUS_OUT's 6
   class-clearance items, the dangling zone via. M2's bar (BRIEF §7): 0 unconnected but J1's no-connect pair,
   errors only Sofar's copied features with reasons, 0 copper-defect warnings, check_rules clean, pairs within the
   mote's lengths, Kelvin yes.
4. Then M3 (the JLCPCB DFM sweep, BRIEF §6: every limit fetched from JLCPCB's published pages, cited in DFM.md,
   encoded in the design rules) and M4 (REPORT.md per BRIEF §8, renders, the draft PR updated).

I will not answer questions mid-run; decide, record, continue. Stop and write REPORT.md if a hard rule would break
or the board must grow beyond the brief. When M2 is at its bar (and again after M4), send QE round 2 to the standing
S7 QE session ("QE review S7.a layout experiment brief (PR #29)"; docs/PROMPTS.md §5; name your session in the
request so the report comes to you), save each report in qe/, fix and resend until it approves, and tell me the
verdict, the PR link and the pass/fail table. Give me a one-line status after every rebuild, and stop to report if
a milestone stalls after three rebuilds.
```

## Session 2.b — DFM first, then the board grows and the routing is cleaned up (2026-10-08)

Session 2 brought M2 to its bar (QE round 2 APPROVED WITH NITS) and stopped for Nick's review. Nick's decisions are in
`LESSONS.md` §3. Start a new Claude Code session (Fable 5.1, high effort) and paste:

```
Layout experiment 1.a, session 2.b. Read CLAUDE.md, then experiments/fable_layout_01a/BRIEF.md in full (your spec;
its hard rules override anything else), LESSONS.md (Nick's decisions in §3 and the order of work in §4), HANDOFF.md,
REPORT.md, LOG.md "M2, session 2", qe/S7b_01a_round2.md, and look at out/before_after/index.html and
out/review/index.html. Check out experiment/fable-layout-01a (origin, last commit of session 2; never merge; PR #31 is
the draft PR, base experiment/fable-layout-01) and work only inside experiments/fable_layout_01a/. KiCad is closed;
use KiCad 9's bundled Python (pcbnew) and kicad-cli; the pipeline is tools/build_all.sh (first run from m0 on a fresh
checkout; START=m2 after any placement, pour or copy change; START=m4 only for routing-only changes). Never run a
milestone script on a board left by a later step.

Order of work, committing after each with renders and a LOG.md entry:
1. DFM rules first (BRIEF §6): fetch every JLCPCB limit from their published capabilities and 6-layer stackup pages
   during the run, cite URL and date per row in DFM.md, encode each in .kicad_pro / .kicad_dru (or a script where DRC
   cannot), run DRC on the board as it is and report what the real rules say about it. No board edit before this.
2. Board 49 x 68 mm (3 mm wider, 3 mm taller; Nick 2026-10-08, supersedes the brief's 2 mm south allowance): move the
   frame, the fixed items and the keep-outs (geom.py, m1_fixed.py, check_fixed.py), and record where the extra width
   and height go (OPTIONS.md addendum). Move the threaded inserts 1-2 mm toward the west wall: the mote's corner
   inserts sit 3.5 mm centre-to-edge with the ring copper at the outline; decide the shift from JLCPCB's edge figure
   and the brief's 0.5 mm, state what it buys, keep Sofar's 4.8 mm keep-out. Then an OPTIONS addendum, as M0 did:
   U1 in the CENTRE of the widened band between the inductor envelopes (Nick: the ADIN belongs in the middle, central
   to the inductors and the header and away from the edge where strain and deflection concentrate; it fits once the
   band is ~11 mm) versus U1 in the west pocket, each tried through M2 on a scratch copy, with pair lengths, SPI
   lengths, courtyards and the exits' occupancy side by side. The centre is the preferred answer; keep the pocket only
   if the trial shows the centre cannot meet the bar, and say why in numbers (LESSONS section 3). In the same
   placement pass put both cut jumpers (JP1 5 V to the Pi, JP2 LED supply) on the TOP side near a board edge with no
   tall part beside them, visible and cuttable (Nick); state what their nets' routing costs.
3. Router clean-up: 45 degree runs as single segments (merge collinear steps in Grid.polyline and commit_pair), no
   back-and-forth; keep every pair under the mote's length with margin (BM1_DATA_P had 0.04 mm).
4. Corridors reserved before routing: SPI (SCK, MOSI, MISO, ~{CS}) on a reserved Internal 2 lane straight from U1 to
   J1's SPI pins, routed first, never along the west edge (SPI is critical; length matching is not required, LESSONS
   §5); then the fan-out vias, the pairs, the rest.
5. Rebuild from M1, all checks (check_fixed, blockcheck, check_rules, drc_summary, drcexclude, test_pair), renders,
   tools/review_views.py and tools/before_after.py (before = session 2's final board b22752f), REPORT.md per BRIEF §8
   with the DFM table, the draft PR updated.

I will not answer questions mid-run; decide, record, continue. Stop and write REPORT.md if a hard rule would break.
After every rebuild give me a one-line status and regenerate the before/after page; stop to report if a milestone
stalls after three rebuilds. When M3 is at its bar, send QE round 3 to the standing S7 QE session ("QE review S7.a
layout experiment brief (PR #29)"; docs/PROMPTS.md section 5; name your session in the request), save the report in
qe/, fix and resend until it approves, then publish the design review (mote vs board per region, before vs after) and
stop for my review.
```
