nickraymond/nereus_Pi_shield_ADIN2111/experiments/fable_layout_01/out/m0/drc_summary.txt

violations: 288 {('items_not_allowed', 'error'): 2, ('clearance', 'error'): 25, ('shorting_items', 'error'): 7, ('hole_clearance', 'error'): 29, ('courtyards_overlap', 'error'): 7, ('padstack_invalid', 'error'): 4, ('invalid_outline', 'error'): 1, ('solder_mask_bridge', 'error'): 39, ('padstack', 'warning'): 38, ('hole_to_hole', 'warning'): 4, ('lib_footprint_mismatch', 'warning'): 4, ('text_height', 'warning'): 112, ('text_thickness', 'warning'): 4, ('silk_over_copper', 'warning'): 8, ('silk_overlap', 'warning'): 2, ('nonmirrored_text_on_back_layer', 'warning'): 2}
unconnected_items: 257 {('unconnected_items', 'error'): 257}
schematic_parity: 4 {('net_conflict', 'warning'): 4}
  parity: No pad found for pin 1 (/Top-Level Schematic/BM1_P) in schematic. | Footprint MP1
  parity: No pad found for pin 1 (/Top-Level Schematic/BM1_N) in schematic. | Footprint MP2
  parity: No pad found for pin 1 (/Top-Level Schematic/BM2_P) in schematic. | Footprint MP3
  parity: No pad found for pin 1 (/Top-Level Schematic/BM2_N) in schematic. | Footprint MP4
