nickraymond/nereus_Pi_shield_ADIN2111/experiments/fable_layout_01/out/m1/drc_summary.txt

18 ('clearance', 'error', 'parked')
2 ('courtyards_overlap', 'error', 'placed')
36 ('hole_clearance', 'error', 'placed')
8 ('lib_footprint_mismatch', 'warning', 'placed')
2 ('nonmirrored_text_on_back_layer', 'warning', 'parked')
34 ('padstack', 'warning', 'parked')
4 ('padstack', 'warning', 'placed')
4 ('padstack_invalid', 'error', 'placed')
28 ('shorting_items', 'error', 'placed')
2 ('silk_edge_clearance', 'warning', 'placed')
1 ('silk_over_copper', 'warning', 'placed')
1 ('silk_overlap', 'warning', 'parked')
4 ('solder_mask_bridge', 'error', 'parked')
8 ('solder_mask_bridge', 'error', 'placed')
106 ('text_height', 'warning', 'parked')
6 ('text_height', 'warning', 'placed')
4 ('text_thickness', 'warning', 'parked')
unconnected_items: 261
schematic_parity: 4
