nickraymond/nereus_Pi_shield_ADIN2111/experiments/fable_layout_01a/out/m1/drc_summary.txt

4 ('clearance', 'error')
12 ('courtyards_overlap', 'error')
36 ('hole_clearance', 'error')
8 ('lib_footprint_mismatch', 'warning')
2 ('nonmirrored_text_on_back_layer', 'warning')
38 ('padstack', 'warning')
4 ('padstack_invalid', 'error')
28 ('shorting_items', 'error')
8 ('silk_edge_clearance', 'warning')
40 ('silk_over_copper', 'warning')
42 ('silk_overlap', 'warning')
12 ('solder_mask_bridge', 'error')
112 ('text_height', 'warning')
4 ('text_thickness', 'warning')
unconnected_items: 261
schematic_parity: 4
errors: 96  warnings: 254
open: Pad 1 [/Top-Level Schematic/5V_PI] of R37 on 6 Bottom Layer | Pad 2 [/Top-Level Schematic/5V_PI] of C57 on 6 Bottom Layer
open: Pad 2 [/Top-Level Schematic/5V_PI] of C56 on 6 Bottom Layer | Pad 2 [/Top-Level Schematic/5V_PI] of C57 on 6 Bottom Layer
open: Pad 2 [/Top-Level Schematic/5V_PI] of C57 on 6 Bottom Layer | Pad 1 [/Top-Level Schematic/5V_PI] of C58 on 6 Bottom Layer
open: Pad 2 [/Top-Level Schematic/5V_PI] of JP1 on Top Layer | Pad 2 [/Top-Level Schematic/5V_PI] of C56 on 6 Bottom Layer
open: Pad 2 [/Top-Level Schematic/5V_PI] of L6 on Top Layer | Pad 1 [/Top-Level Schematic/5V_PI] of TP38 on 6 Bottom Layer
open: Pad 2 [/Top-Level Schematic/5V_PI] of L6 on Top Layer | Pad 1 [/Top-Level Schematic/5V_PI] of C58 on 6 Bottom Layer
open: Pad 35 [/Top-Level Schematic/ADIN/ADIN_AVDD] of U1 on Top Layer | Pad 1 [/Top-Level Schematic/ADIN/ADIN_AVDD] of C12 on 6 Bottom Layer
open: Pad 35 [/Top-Level Schematic/ADIN/ADIN_AVDD] of U1 on Top Layer | Pad 36 [/Top-Level Schematic/ADIN/ADIN_AVDD] of U1 on Top Layer
open: Pad 6 [/Top-Level Schematic/ADIN/ADIN_AVDD] of U1 on Top Layer | Pad 1 [/Top-Level Schematic/ADIN/ADIN_AVDD] of C9 on 6 Bottom Layer
open: Pad 1 [/Top-Level Schematic/ADIN/ADIN_AVDD] of C9 on 6 Bottom Layer | Pad 7 [/Top-Level Schematic/ADIN/ADIN_AVDD] of U1 on Top Layer
open: Pad A1 [/Top-Level Schematic/ADIN/ADIN_AVDD] of U2 on 6 Bottom Layer | Pad 1 [/Top-Level Schematic/ADIN/ADIN_AVDD] of C9 on 6 Bottom Layer
open: Pad 30 [/Top-Level Schematic/ADIN/ADIN_AVDD] of U1 on Top Layer | Pad 29 [/Top-Level Schematic/ADIN/ADIN_AVDD] of U1 on Top Layer
open: Pad 30 [/Top-Level Schematic/ADIN/ADIN_AVDD] of U1 on Top Layer | Pad 1 [/Top-Level Schematic/ADIN/ADIN_AVDD] of C12 on 6 Bottom Layer
open: Pad 29 [/Top-Level Schematic/ADIN/ADIN_AVDD] of U1 on Top Layer | Pad 1 [/Top-Level Schematic/ADIN/ADIN_AVDD] of C11 on 6 Bottom Layer
open: Pad 12 [/Top-Level Schematic/ADIN/ADIN_AVDD] of U1 on Top Layer | Pad 7 [/Top-Level Schematic/ADIN/ADIN_AVDD] of U1 on Top Layer
open: Pad 13 [/Top-Level Schematic/ADIN/ADIN_AVDD] of U1 on Top Layer | Pad 1 [/Top-Level Schematic/ADIN/ADIN_AVDD] of C10 on 6 Bottom Layer
open: Pad 13 [/Top-Level Schematic/ADIN/ADIN_AVDD] of U1 on Top Layer | Pad 1 [/Top-Level Schematic/ADIN/ADIN_AVDD] of C11 on 6 Bottom Layer
open: Pad 1 [/Top-Level Schematic/ADIN/ADIN_AVDD] of C10 on 6 Bottom Layer | Pad 12 [/Top-Level Schematic/ADIN/ADIN_AVDD] of U1 on Top Layer
open: Pad 1 [/Top-Level Schematic/ADIN/ADIN_AVDD] of TP1 on 6 Bottom Layer | Pad 1 [/Top-Level Schematic/ADIN/ADIN_AVDD] of C10 on 6 Bottom Layer
open: Pad 1 [/Top-Level Schematic/ADIN/ADIN_CLK25_REF] of U1 on Top Layer | Pad 22 [/Top-Level Schematic/ADIN/ADIN_CLK25_REF] of U1 on Top Layer
open: Pad 2 [/Top-Level Schematic/ADIN/ADIN_LED_VDD] of R46 on 6 Bottom Laye | Pad 2 [/Top-Level Schematic/ADIN/ADIN_LED_VDD] of JP2 on 6 Bottom Laye
open: Pad 2 [/Top-Level Schematic/ADIN/ADIN_LED_VDD] of R44 on 6 Bottom Laye | Pad 2 [/Top-Level Schematic/ADIN/ADIN_LED_VDD] of JP2 on 6 Bottom Laye
open: Pad 2 [/Top-Level Schematic/ADIN/ADIN_LED_VDD] of R45 on 6 Bottom Laye | Pad 2 [/Top-Level Schematic/ADIN/ADIN_LED_VDD] of R44 on 6 Bottom Laye
open: Pad 37 [/Top-Level Schematic/ADIN/DVDD1_1P1] of U1 on Top Layer | Pad 1 [/Top-Level Schematic/ADIN/DVDD1_1P1] of C6 on 6 Bottom Layer
open: Pad 38 [/Top-Level Schematic/ADIN/DVDD1_1P1] of U1 on Top Layer | Pad 37 [/Top-Level Schematic/ADIN/DVDD1_1P1] of U1 on Top Layer
open: Pad 14 [/Top-Level Schematic/ADIN/DVDD2_1P1] of U1 on Top Layer | Pad 1 [/Top-Level Schematic/ADIN/DVDD2_1P1] of C5 on 6 Bottom Layer
open: Pad 1 [/Top-Level Schematic/ADIN/DVDD2_1P1] of C5 on 6 Bottom Layer | Pad 15 [/Top-Level Schematic/ADIN/DVDD2_1P1] of U1 on Top Layer
open: Pad 21 [/Top-Level Schematic/ADIN/~{ADIN_P1_LED1}] of U1 on Top Layer | Pad 1 [/Top-Level Schematic/ADIN/~{ADIN_P1_LED1}] of R3 on 6 Bottom La
open: Pad 1 [/Top-Level Schematic/ADIN/~{ADIN_P1_LED1}] of R3 on 6 Bottom La | Pad 1 [/Top-Level Schematic/ADIN/~{ADIN_P1_LED1}] of D9 on Top Layer
open: Pad 48 [/Top-Level Schematic/ADIN/~{ADIN_P2_LED1}] of U1 on Top Layer | Pad 1 [/Top-Level Schematic/ADIN/~{ADIN_P2_LED1}] of R5 on 6 Bottom La
open: Pad 1 [/Top-Level Schematic/ADIN/~{ADIN_P2_LED1}] of D10 on Top Layer | Pad 48 [/Top-Level Schematic/ADIN/~{ADIN_P2_LED1}] of U1 on Top Layer
open: Pad 43 [/Top-Level Schematic/ADIN_MISO] of U1 on Top Layer | PTH pad 21 [/Top-Level Schematic/ADIN_MISO] of J1
open: Pad 42 [/Top-Level Schematic/ADIN_MOSI] of U1 on Top Layer | PTH pad 19 [/Top-Level Schematic/ADIN_MOSI] of J1
open: Pad B2 [/Top-Level Schematic/ADIN_PWR] of U3 on 6 Bottom Layer | Pad B2 [/Top-Level Schematic/ADIN_PWR] of U2 on 6 Bottom Layer
open: Pad 1 [/Top-Level Schematic/ADIN_PWR] of R43 on 6 Bottom Layer | Pad B2 [/Top-Level Schematic/ADIN_PWR] of U2 on 6 Bottom Layer
open: Pad 1 [/Top-Level Schematic/ADIN_PWR] of TP8 on 6 Bottom Layer | Pad 1 [/Top-Level Schematic/ADIN_PWR] of R43 on 6 Bottom Layer
open: Pad 1 [/Top-Level Schematic/ADIN_PWR] of TP8 on 6 Bottom Layer | PTH pad 16 [/Top-Level Schematic/ADIN_PWR] of J1
open: Pad 44 [/Top-Level Schematic/ADIN_SCK] of U1 on Top Layer | PTH pad 23 [/Top-Level Schematic/ADIN_SCK] of J1
open: Pad 27 [/Top-Level Schematic/BM1_DATA_N] of U1 on Top Layer | Pad 2 [/Top-Level Schematic/BM1_DATA_N] of T1 on Top Layer
open: Pad 28 [/Top-Level Schematic/BM1_DATA_P] of U1 on Top Layer | Pad 1 [/Top-Level Schematic/BM1_DATA_P] of T1 on Top Layer
open: Via [/Top-Level Schematic/BM1_N] on Top Layer - 6 Bottom Layer | Pad 2 [/Top-Level Schematic/BM1_N] of L1 on Top Layer
open: Pad 7 [/Top-Level Schematic/BM1_N] of T1 on Top Layer | Pad 2 [/Top-Level Schematic/BM1_N] of D4 on 6 Bottom Layer
open: Pad 2 [/Top-Level Schematic/BM1_N] of D4 on 6 Bottom Layer | Pad 2 [/Top-Level Schematic/BM1_N] of R13 on 6 Bottom Layer
open: Pad 2 [/Top-Level Schematic/BM1_N] of L1 on Top Layer | Pad 2 [/Top-Level Schematic/BM1_N] of R13 on 6 Bottom Layer
open: Pad 2 [/Top-Level Schematic/BM1_N] of R13 on 6 Bottom Layer | Pad 1 [/Top-Level Schematic/BM1_N] of TP5 on 6 Bottom Layer
open: Via [/Top-Level Schematic/BM1_P] on Top Layer - 6 Bottom Layer | Pad 1 [/Top-Level Schematic/BM1_P] of D4 on 6 Bottom Layer
open: Pad 1 [/Top-Level Schematic/BM1_P] of TP3 on 6 Bottom Layer | Pad 6 [/Top-Level Schematic/BM1_P] of T1 on Top Layer
open: Pad 1 [/Top-Level Schematic/BM1_P] of D4 on 6 Bottom Layer | Pad 3 [/Top-Level Schematic/BM1_P] of L1 on Top Layer
open: Pad 1 [/Top-Level Schematic/BM1_P] of R12 on 6 Bottom Layer | Pad 3 [/Top-Level Schematic/BM1_P] of L1 on Top Layer
open: Pad 1 [/Top-Level Schematic/BM1_P] of R12 on 6 Bottom Layer | Pad 1 [/Top-Level Schematic/BM1_P] of TP3 on 6 Bottom Layer
open: Pad 4 [/Top-Level Schematic/BM2_DATA_N] of U1 on Top Layer | Pad 2 [/Top-Level Schematic/BM2_DATA_N] of T2 on Top Layer
open: Pad 5 [/Top-Level Schematic/BM2_DATA_P] of U1 on Top Layer | Pad 1 [/Top-Level Schematic/BM2_DATA_P] of T2 on Top Layer
open: Via [/Top-Level Schematic/BM2_N] on Top Layer - 6 Bottom Layer | Pad 2 [/Top-Level Schematic/BM2_N] of D5 on 6 Bottom Layer
open: Pad 2 [/Top-Level Schematic/BM2_N] of L2 on Top Layer | Pad 2 [/Top-Level Schematic/BM2_N] of R19 on 6 Bottom Layer
open: Pad 1 [/Top-Level Schematic/BM2_N] of TP13 on 6 Bottom Layer | Pad 2 [/Top-Level Schematic/BM2_N] of R19 on 6 Bottom Layer
open: Pad 1 [/Top-Level Schematic/BM2_N] of TP13 on 6 Bottom Layer | Pad 2 [/Top-Level Schematic/BM2_N] of D5 on 6 Bottom Layer
open: Pad 7 [/Top-Level Schematic/BM2_N] of T2 on Top Layer | Pad 2 [/Top-Level Schematic/BM2_N] of R19 on 6 Bottom Layer
open: Pad 1 [/Top-Level Schematic/BM2_P] of D5 on 6 Bottom Layer | Pad 1 [/Top-Level Schematic/BM2_P] of TP7 on 6 Bottom Layer
open: Pad 1 [/Top-Level Schematic/BM2_P] of D5 on 6 Bottom Layer | Pad 6 [/Top-Level Schematic/BM2_P] of T2 on Top Layer
open: Pad 1 [/Top-Level Schematic/BM2_P] of R17 on 6 Bottom Layer | Pad 3 [/Top-Level Schematic/BM2_P] of L2 on Top Layer
open: Pad 1 [/Top-Level Schematic/BM2_P] of R17 on 6 Bottom Layer | Pad 1 [/Top-Level Schematic/BM2_P] of TP7 on 6 Bottom Layer
open: Pad 1 [/Top-Level Schematic/BM2_P] of R17 on 6 Bottom Layer | Via [/Top-Level Schematic/BM2_P] on Top Layer - 6 Bottom Layer
open: PTH pad 5 [/Top-Level Schematic/I2C1_SCL] of J1 | Pad 5 [/Top-Level Schematic/I2C1_SCL] of U4 on 6 Bottom Layer
open: Pad 1 [/Top-Level Schematic/I2C1_SCL] of R26 on 6 Bottom Layer | PTH pad 5 [/Top-Level Schematic/I2C1_SCL] of J1
open: PTH pad 3 [/Top-Level Schematic/I2C1_SDA] of J1 | Pad 6 [/Top-Level Schematic/I2C1_SDA] of U4 on 6 Bottom Layer
open: Pad 1 [/Top-Level Schematic/I2C1_SDA] of R27 on 6 Bottom Layer | PTH pad 3 [/Top-Level Schematic/I2C1_SDA] of J1
open: Pad 2 [/Top-Level Schematic/Load Switch/ISET] of R34 on Top Layer | Pad 7 [/Top-Level Schematic/Load Switch/ISET] of U11 on Top Layer
open: Pad 1 [/Top-Level Schematic/PAYLOAD_EN] of TP19 on 6 Bottom Layer | PTH pad 36 [/Top-Level Schematic/PAYLOAD_EN] of J1
open: Pad 1 [/Top-Level Schematic/PAYLOAD_EN] of TP19 on 6 Bottom Layer | Pad 4 [/Top-Level Schematic/PAYLOAD_EN] of U11 on Top Layer
open: Pad 4 [/Top-Level Schematic/PAYLOAD_EN] of U11 on Top Layer | Pad 1 [/Top-Level Schematic/PAYLOAD_EN] of R42 on 6 Bottom Layer
open: PTH pad 2 [/Top-Level Schematic/PI_5V] of J1 | PTH pad 4 [/Top-Level Schematic/PI_5V] of J1
open: Pad 1 [/Top-Level Schematic/PI_5V] of JP1 on Top Layer | PTH pad 2 [/Top-Level Schematic/PI_5V] of J1
open: Pad 1 [/Top-Level Schematic/PoDL/Power Monitor/P_IN] of L2 on Top Laye | Pad 1 [/Top-Level Schematic/PoDL/Power Monitor/P_IN] of C26 on 6 Botto
open: Pad 2 [/Top-Level Schematic/PoDL/Power Monitor/P_IN] of R8 on 6 Bottom | Pad 1 [/Top-Level Schematic/PoDL/Power Monitor/P_IN] of U4 on 6 Bottom
open: Pad 2 [/Top-Level Schematic/PoDL/Power Monitor/P_IN] of R8 on 6 Bottom | Pad 1 [/Top-Level Schematic/PoDL/Power Monitor/P_IN] of L2 on Top Laye
open: Pad 1 [/Top-Level Schematic/PoDL/Power Monitor/P_IN] of U4 on 6 Bottom | Pad 2 [/Top-Level Schematic/PoDL/Power Monitor/P_IN] of R17 on 6 Botto
open: Pad 2 [/Top-Level Schematic/Power Regulators/3V3_Buck_SW] of U5 on Top | Pad 1 [/Top-Level Schematic/Power Regulators/3V3_Buck_SW] of C28 on 6 
open: Pad 1 [/Top-Level Schematic/Power Regulators/3V3_Buck_SW] of L3 on Top | Pad 2 [/Top-Level Schematic/Power Regulators/3V3_Buck_SW] of U5 on Top
open: Pad 4 [/Top-Level Schematic/Power Regulators/3V3_FB] of U5 on Top Laye | Pad 1 [/Top-Level Schematic/Power Regulators/3V3_FB] of R23 on 6 Botto
open: Pad 1 [/Top-Level Schematic/Power Regulators/3V3_FB] of R23 on 6 Botto | Pad 2 [/Top-Level Schematic/Power Regulators/3V3_FB] of R21 on 6 Botto
open: Pad 5 [/Top-Level Schematic/Power Regulators/3V3_UVLO] of U5 on Top La | Pad 1 [/Top-Level Schematic/Power Regulators/3V3_UVLO] of R20 on 6 Bot
open: Pad 1 [/Top-Level Schematic/Power Regulators/3V3_UVLO] of R20 on 6 Bot | Pad 2 [/Top-Level Schematic/Power Regulators/3V3_UVLO] of R22 on 6 Bot
open: Pad 2 [/Top-Level Schematic/Power Regulators/5V_Buck_SW] of U10 on Top | Pad 1 [/Top-Level Schematic/Power Regulators/5V_Buck_SW] of C53 on 6 B
open: Pad 1 [/Top-Level Schematic/Power Regulators/5V_Buck_SW] of L6 on Top  | Pad 2 [/Top-Level Schematic/Power Regulators/5V_Buck_SW] of U10 on Top
open: Pad 4 [/Top-Level Schematic/Power Regulators/5V_FB] of U10 on Top Laye | Pad 1 [/Top-Level Schematic/Power Regulators/5V_FB] of R38 on 6 Bottom
open: Pad 1 [/Top-Level Schematic/Power Regulators/5V_FB] of R38 on 6 Bottom | Pad 2 [/Top-Level Schematic/Power Regulators/5V_FB] of R37 on 6 Bottom
open: Pad 5 [/Top-Level Schematic/Power Regulators/5V_UVLO] of U10 on Top La | Pad 1 [/Top-Level Schematic/Power Regulators/5V_UVLO] of R39 on 6 Bott
open: Pad 1 [/Top-Level Schematic/Power Regulators/5V_UVLO] of R39 on 6 Bott | Pad 2 [/Top-Level Schematic/Power Regulators/5V_UVLO] of R40 on 6 Bott
open: Pad 45 [/Top-Level Schematic/~{ADIN_CS}] of U1 on Top Layer | PTH pad 24 [/Top-Level Schematic/~{ADIN_CS}] of J1
open: Pad 39 [/Top-Level Schematic/~{ADIN_INT}] of U1 on Top Layer | Pad 1 [/Top-Level Schematic/~{ADIN_INT}] of R1 on 6 Bottom Layer
open: Pad 1 [/Top-Level Schematic/~{ADIN_INT}] of R1 on 6 Bottom Layer | PTH pad 22 [/Top-Level Schematic/~{ADIN_INT}] of J1
open: Pad 20 [/Top-Level Schematic/~{ADIN_RST}] of U1 on Top Layer | PTH pad 18 [/Top-Level Schematic/~{ADIN_RST}] of J1
open: Pad 1 [/Top-Level Schematic/~{PAYLOAD_FAULT}] of R35 on 6 Bottom Layer | PTH pad 38 [/Top-Level Schematic/~{PAYLOAD_FAULT}] of J1
open: Pad 1 [/Top-Level Schematic/~{PAYLOAD_FAULT}] of R35 on 6 Bottom Layer | Pad 1 [/Top-Level Schematic/~{PAYLOAD_FAULT}] of TP35 on 6 Bottom Laye
open: Pad 9 [/Top-Level Schematic/~{PAYLOAD_FAULT}] of U11 on Top Layer | Pad 1 [/Top-Level Schematic/~{PAYLOAD_FAULT}] of R35 on 6 Bottom Layer
open: Pad 2 [1V8] of L4 on 6 Bottom Layer | Pad 1 [1V8] of C32 on 6 Bottom Layer
open: Pad 2 [1V8] of L4 on 6 Bottom Layer | Pad A2 [1V8] of U6 on 6 Bottom Layer
open: Pad A2 [1V8] of U6 on 6 Bottom Layer | Pad 1 [1V8] of TP21 on 6 Bottom Layer
open: Pad A2 [1V8] of U6 on 6 Bottom Layer | Pad A2 [1V8] of U2 on 6 Bottom Layer
open: Pad 1 [3V3] of C33 on 6 Bottom Layer | Pad A2 [3V3] of U3 on 6 Bottom Layer
open: Pad C1 [3V3] of U6 on 6 Bottom Layer | Pad B1 [3V3] of U6 on 6 Bottom Layer
open: Pad C1 [3V3] of U6 on 6 Bottom Layer | Pad 1 [3V3] of C33 on 6 Bottom Layer
open: Pad 7 [3V3] of U4 on 6 Bottom Layer | Pad B1 [3V3] of U6 on 6 Bottom Layer
open: Pad 4 [3V3] of U4 on 6 Bottom Layer | Pad 2 [3V3] of C15 on 6 Bottom Layer
open: Pad 4 [3V3] of U4 on 6 Bottom Layer | Pad 1 [3V3] of R7 on 6 Bottom Layer
open: Pad 1 [3V3] of R7 on 6 Bottom Layer | Pad 7 [3V3] of U4 on 6 Bottom Layer
open: Pad 2 [3V3] of R35 on 6 Bottom Layer | Pad 1 [3V3] of R21 on 6 Bottom Layer
open: Pad 1 [3V3] of R21 on 6 Bottom Layer | Pad B1 [3V3] of U6 on 6 Bottom Layer
open: Pad 2 [3V3] of L3 on Top Layer | Pad 2 [3V3] of C31 on Top Layer
open: Pad 1 [3V3] of TP20 on 6 Bottom Layer | Pad 2 [3V3] of R26 on 6 Bottom Layer
open: Pad 2 [3V3] of R26 on 6 Bottom Layer | Pad 2 [3V3] of R27 on 6 Bottom Layer
open: Pad 2 [3V3] of R27 on 6 Bottom Layer | Pad 2 [3V3] of L3 on Top Layer
open: Pad 2 [3V3] of C31 on Top Layer | Pad 1 [3V3] of R21 on 6 Bottom Layer
open: Pad 2 [ADIN_VDDIO] of R1 on 6 Bottom Layer | Pad 2 [ADIN_VDDIO] of R6 on 6 Bottom Layer
open: Pad 1 [ADIN_VDDIO] of C14 on 6 Bottom Layer | Pad 46 [ADIN_VDDIO] of U1 on Top Layer
open: Pad 1 [ADIN_VDDIO] of C14 on 6 Bottom Layer | Pad 2 [ADIN_VDDIO] of R6 on 6 Bottom Layer
open: Pad 46 [ADIN_VDDIO] of U1 on Top Layer | Pad 2 [ADIN_VDDIO] of R5 on 6 Bottom Layer
open: Pad 2 [ADIN_VDDIO] of R6 on 6 Bottom Layer | Pad 18 [ADIN_VDDIO] of U1 on Top Layer
open: Pad 2 [ADIN_VDDIO] of R5 on 6 Bottom Layer | Pad A1 [ADIN_VDDIO] of U3 on 6 Bottom Layer
open: Pad 18 [ADIN_VDDIO] of U1 on Top Layer | Pad 1 [ADIN_VDDIO] of C13 on 6 Bottom Layer
open: Pad 1 [ADIN_VDDIO] of C13 on 6 Bottom Layer | Pad 1 [ADIN_VDDIO] of TP2 on 6 Bottom Layer
open: Pad 1 [ADIN_VDDIO] of TP2 on 6 Bottom Layer | Pad 2 [ADIN_VDDIO] of R3 on 6 Bottom Layer
open: Pad 1 [ADIN_VDDIO] of JP2 on 6 Bottom Layer | Pad 2 [ADIN_VDDIO] of R3 on 6 Bottom Layer
open: Pad 2 [GND] of C6 on 6 Bottom Layer | Pad 2 [GND] of C12 on 6 Bottom Layer
open: Pad 2 [GND] of C14 on 6 Bottom Layer | Pad 2 [GND] of R4 on 6 Bottom Layer
open: Pad 2 [GND] of R4 on 6 Bottom Layer | Pad B1 [GND] of U3 on 6 Bottom Layer
open: Pad 2 [GND] of C4 on 6 Bottom Layer | Pad 2 [GND] of C12 on 6 Bottom Layer
open: Pad 2 [GND] of C4 on 6 Bottom Layer | Pad 2 [GND] of C3 on 6 Bottom Layer
open: Pad 2 [GND] of C9 on 6 Bottom Layer | Pad 2 [GND] of C1 on 6 Bottom Layer
open: Pad 2 [GND] of C9 on 6 Bottom Layer | Pad B1 [GND] of U3 on 6 Bottom Layer
open: Pad 2 [GND] of C3 on 6 Bottom Layer | Pad 49 [GND] of U1 on Top Layer
open: Pad 2 [GND] of C1 on 6 Bottom Layer | Pad 2 [GND] of C2 on 6 Bottom Layer
open: Pad 2 [GND] of C1 on 6 Bottom Layer | Pad B1 [GND] of U2 on 6 Bottom Layer
open: Pad 2 [GND] of C11 on 6 Bottom Layer | Pad 2 [GND] of C3 on 6 Bottom Layer
open: Pad 2 [GND] of C7 on 6 Bottom Layer | Pad 2 [GND] of C11 on 6 Bottom Layer
open: Pad 2 [GND] of C5 on 6 Bottom Layer | Pad 2 [GND] of C10 on 6 Bottom Layer
open: Pad 2 [GND] of R2 on 6 Bottom Layer | Pad 2 [GND] of C13 on 6 Bottom Layer
open: Pad 2 [GND] of R2 on 6 Bottom Layer | Pad 2 [GND] of C11 on 6 Bottom Layer
open: Pad 2 [GND] of C13 on 6 Bottom Layer | Pad 2 [GND] of C5 on 6 Bottom Layer
open: Pad 2 [GND] of C10 on 6 Bottom Layer | Pad 2 [GND] of C2 on 6 Bottom Layer
open: Pad 4 [GND] of Y1 on 6 Bottom Layer | Pad 2 [GND] of C7 on 6 Bottom Layer
open: Pad 4 [GND] of Y1 on 6 Bottom Layer | Pad 2 [GND] of Y1 on 6 Bottom Layer
open: Pad 2 [GND] of C8 on 6 Bottom Layer | Pad 2 [GND] of Y1 on 6 Bottom Layer
open: Pad 1 [GND] of C18 on 6 Bottom Layer | Pad 2 [GND] of C8 on 6 Bottom Layer
open: Pad 1 [GND] of C18 on 6 Bottom Layer | Pad 1 [GND] of C19 on 6 Bottom Layer
open: Pad 2 [GND] of R43 on 6 Bottom Layer | Pad 1 [GND] of C18 on 6 Bottom Layer
open: Pad 1 [GND] of R13 on 6 Bottom Layer | Pad 2 [GND] of C17 on 6 Bottom Layer
open: Pad 2 [GND] of C21 on Top Layer | Pad 1 [GND] of TP23 on 6 Bottom Layer
open: Pad 1 [GND] of R19 on 6 Bottom Layer | Pad 1 [GND] of C19 on 6 Bottom Layer
open: Pad 2 [GND] of C20 on 6 Bottom Layer | Pad 1 [GND] of TP23 on 6 Bottom Layer
open: Pad 2 [GND] of C20 on 6 Bottom Layer | Pad 2 [GND] of J5 on Top Layer
open: Pad 1 [GND] of C25 on 6 Bottom Layer | Pad 1 [GND] of C27 on 6 Bottom Layer
open: Pad 1 [GND] of C25 on 6 Bottom Layer | Pad 2 [GND] of R43 on 6 Bottom Layer
open: Pad 1 [GND] of C27 on 6 Bottom Layer | Pad 2 [GND] of C33 on 6 Bottom Layer
open: Pad 1 [GND] of D8 on Top Layer | Pad 4 [GND] of L2 on Top Layer
open: Pad 4 [GND] of L1 on Top Layer | Pad 1 [GND] of C25 on 6 Bottom Layer
open: Pad 4 [GND] of L1 on Top Layer | Pad 2 [GND] of D2 on 6 Bottom Layer
open: Pad 2 [GND] of J5 on Top Layer | Pad 1 [GND] of D1 on Top Layer
open: Pad 2 [GND] of D2 on 6 Bottom Layer | Pad 2 [GND] of C17 on 6 Bottom Layer
open: Pad 2 [GND] of C33 on 6 Bottom Layer | Pad A1 [GND] of U6 on 6 Bottom Layer
open: Pad A1 [GND] of U6 on 6 Bottom Layer | Pad C2 [GND] of U6 on 6 Bottom Layer
open: Pad A1 [GND] of U6 on 6 Bottom Layer | Pad 2 [GND] of C32 on 6 Bottom Layer
open: Pad 1 [GND] of C15 on 6 Bottom Layer | Pad 4 [GND] of L2 on Top Layer
open: Pad 3 [GND] of U4 on 6 Bottom Layer | Pad 1 [GND] of C15 on 6 Bottom Layer
open: Pad 3 [GND] of U4 on 6 Bottom Layer | PTH pad 9 [GND] of J1
open: Pad 2 [GND] of C32 on 6 Bottom Layer | Pad 2 [GND] of C26 on 6 Bottom Layer
open: PTH pad 39 [GND] of J1 | Pad 1 [GND] of R34 on Top Layer
open: PTH pad 39 [GND] of J1 | Pad 1 [GND] of D1 on Top Layer
open: PTH pad 14 [GND] of J1 | Pad 2 [GND] of R38 on 6 Bottom Layer
open: PTH pad 14 [GND] of J1 | Pad 2 [GND] of C30 on Top Layer
open: PTH pad 20 [GND] of J1 | Pad 2 [GND] of C30 on Top Layer
open: PTH pad 20 [GND] of J1 | Pad 2 [GND] of C32 on 6 Bottom Layer
open: PTH pad 30 [GND] of J1 | Pad 1 [GND] of C23 on Top Layer
open: PTH pad 30 [GND] of J1 | PTH pad 34 [GND] of J1
open: PTH pad 30 [GND] of J1 | PTH pad 25 [GND] of J1
open: Pad 2 [GND] of C55 on Top Layer | Pad 2 [GND] of C54 on 6 Bottom Layer
open: Pad 2 [GND] of C55 on Top Layer | Pad 1 [GND] of C57 on 6 Bottom Layer
open: Pad 2 [GND] of C55 on Top Layer | PTH pad 9 [GND] of J1
open: Pad 2 [GND] of C54 on 6 Bottom Layer | Pad 1 [GND] of U10 on Top Layer
open: Pad 2 [GND] of C29 on 6 Bottom Layer | Pad 2 [GND] of C30 on Top Layer
open: Pad 1 [GND] of C56 on 6 Bottom Layer | PTH pad 6 [GND] of J1
open: Pad 1 [GND] of C57 on 6 Bottom Layer | Pad 1 [GND] of C56 on 6 Bottom Layer
open: Pad 2 [GND] of R23 on 6 Bottom Layer | Pad 1 [GND] of U5 on Top Layer
open: Pad 1 [GND] of C22 on Top Layer | PTH pad 34 [GND] of J1
open: Pad 6 [GND] of U11 on Top Layer | Pad 1 [GND] of R34 on Top Layer
open: Pad 3 [GND] of U11 on Top Layer | Pad 5 [GND] of U11 on Top Layer
open: Pad 3 [GND] of U11 on Top Layer | Pad 11 [GND] of U11 on Top Layer
open: Pad 11 [GND] of U11 on Top Layer | Pad 6 [GND] of U11 on Top Layer
open: Pad 1 [GND] of U10 on Top Layer | Pad 2 [GND] of R38 on 6 Bottom Layer
open: Pad 1 [GND] of U5 on Top Layer | Pad 2 [GND] of C29 on 6 Bottom Layer
open: Pad 2 [GND] of D3 on 6 Bottom Layer | Pad 3 [GND] of U11 on Top Layer
open: Pad 2 [GND] of D3 on 6 Bottom Layer | Pad 1 [GND] of C22 on Top Layer
open: Pad 1 [GND] of R40 on 6 Bottom Layer | Pad 2 [GND] of R38 on 6 Bottom Layer
open: Pad 1 [GND] of R22 on 6 Bottom Layer | Pad 2 [GND] of R23 on 6 Bottom Layer
open: Pad 1 [GND] of R22 on 6 Bottom Layer | Pad 1 [GND] of C23 on Top Layer
open: Pad 2 [GND] of C58 on 6 Bottom Layer | Pad 1 [GND] of C57 on 6 Bottom Layer
open: Pad 2 [GND] of C58 on 6 Bottom Layer | Pad 1 [GND] of TP24 on 6 Bottom Layer
open: Pad 2 [GND] of C49 on Top Layer | Pad 2 [GND] of R42 on 6 Bottom Layer
open: Pad 2 [GND] of C49 on Top Layer | Pad 2 [GND] of D3 on 6 Bottom Layer
open: Pad 1 [GND] of C31 on Top Layer | Pad 1 [GND] of R22 on 6 Bottom Layer
open: Pad 2 [GND] of C50 on 6 Bottom Layer | Pad 2 [GND] of R42 on 6 Bottom Layer
open: Pad 3 [Net-(C16-Pad1)] of T1 on Top Layer | Pad 1 [Net-(C16-Pad1)] of C16 on 6 Bottom Layer
open: Pad 1 [Net-(C16-Pad1)] of R14 on 6 Bottom Layer | Pad 3 [Net-(C16-Pad1)] of T1 on Top Layer
open: Pad 4 [Net-(C16-Pad2)] of T1 on Top Layer | Pad 2 [Net-(C16-Pad2)] of C16 on 6 Bottom Layer
open: Pad 5 [Net-(C18-Pad2)] of T1 on Top Layer | Pad 2 [Net-(C18-Pad2)] of C18 on 6 Bottom Layer
open: Pad 2 [Net-(C19-Pad2)] of R14 on 6 Bottom Layer | Pad 2 [Net-(C19-Pad2)] of C19 on 6 Bottom Layer
open: Pad 2 [Net-(C22-A)] of C22 on Top Layer | Pad 1 [Net-(C22-A)] of R15 on 6 Bottom Layer
open: Pad 1 [Net-(C23-A)] of R16 on Top Layer | Pad 2 [Net-(C23-A)] of C23 on Top Layer
open: Pad 3 [Net-(C24-Pad1)] of T2 on Top Layer | Pad 1 [Net-(C24-Pad1)] of C24 on 6 Bottom Layer
open: Pad 1 [Net-(C24-Pad1)] of R18 on 6 Bottom Layer | Pad 3 [Net-(C24-Pad1)] of T2 on Top Layer
open: Pad 4 [Net-(C24-Pad2)] of T2 on Top Layer | Pad 2 [Net-(C24-Pad2)] of C24 on 6 Bottom Layer
open: Pad 5 [Net-(C25-Pad2)] of T2 on Top Layer | Pad 2 [Net-(C25-Pad2)] of C25 on 6 Bottom Layer
open: Pad 2 [Net-(C27-Pad2)] of R18 on 6 Bottom Layer | Pad 2 [Net-(C27-Pad2)] of C27 on 6 Bottom Layer
open: Pad 2 [Net-(D8-A)] of D8 on Top Layer | Pad 1 [Net-(D8-A)] of R44 on 6 Bottom Layer
open: Pad 2 [Net-(D9-A)] of D9 on Top Layer | Pad 1 [Net-(D9-A)] of R45 on 6 Bottom Layer
open: Pad 1 [Net-(D10-A)] of R46 on 6 Bottom Layer | Pad 2 [Net-(D10-A)] of D10 on Top Layer
open: Pad 1 [Net-(U1A-CEXT_2)] of C1 on 6 Bottom Layer | Pad 9 [Net-(U1A-CEXT_2)] of U1 on Top Layer
open: Pad 10 [Net-(U1A-CEXT_3)] of U1 on Top Layer | Pad 1 [Net-(U1A-CEXT_3)] of C2 on 6 Bottom Layer
open: Pad 32 [Net-(U1A-CEXT_6)] of U1 on Top Layer | Pad 1 [Net-(U1A-CEXT_6)] of C3 on 6 Bottom Layer
open: Pad 33 [Net-(U1A-CEXT_7)] of U1 on Top Layer | Pad 1 [Net-(U1A-CEXT_7)] of C4 on 6 Bottom Layer
open: Pad 1 [Net-(U1A-P1_LED_0/SPI_CFG1)] of R2 on 6 Bottom Layer | Pad 19 [Net-(U1A-P1_LED_0/SPI_CFG1)] of U1 on Top Layer
open: Pad 1 [Net-(U1A-P2_LED_0/P2_SWPD_EN)] of R4 on 6 Bottom Layer | Pad 47 [Net-(U1A-P2_LED_0/P2_SWPD_EN)] of U1 on Top Layer
open: Pad 41 [Net-(U1A-TEST_0/P1_SWPD_EN)] of U1 on Top Layer | Pad 1 [Net-(U1A-TEST_0/P1_SWPD_EN)] of R6 on 6 Bottom Layer
open: Pad 3 [Net-(U1A-XTAL_I/CLK_IN)] of Y1 on 6 Bottom Layer | Pad 23 [Net-(U1A-XTAL_I/CLK_IN)] of U1 on Top Layer
open: Pad 1 [Net-(U1A-XTAL_I/CLK_IN)] of C8 on 6 Bottom Layer | Pad 3 [Net-(U1A-XTAL_I/CLK_IN)] of Y1 on 6 Bottom Layer
open: Pad 1 [Net-(U1A-XTAL_O)] of C7 on 6 Bottom Layer | Pad 24 [Net-(U1A-XTAL_O)] of U1 on Top Layer
open: Pad 1 [Net-(U1A-XTAL_O)] of Y1 on 6 Bottom Layer | Pad 1 [Net-(U1A-XTAL_O)] of C7 on 6 Bottom Layer
open: Pad 8 [Net-(U4-ALERT)] of U4 on 6 Bottom Layer | Pad 2 [Net-(U4-ALERT)] of R7 on 6 Bottom Layer
open: Pad 6 [Net-(U5-CB)] of U5 on Top Layer | Pad 2 [Net-(U5-CB)] of C28 on 6 Bottom Layer
open: Pad 1 [Net-(U6-SW)] of L4 on 6 Bottom Layer | Pad B2 [Net-(U6-SW)] of U6 on 6 Bottom Layer
open: Pad 6 [Net-(U10-CB)] of U10 on Top Layer | Pad 2 [Net-(U10-CB)] of C53 on 6 Bottom Layer
open: Pad 2 [Net-(U11-UVLO)] of U11 on Top Layer | Pad 2 [Net-(U11-UVLO)] of R41 on 6 Bottom Layer
open: Pad 2 [VBUS] of R16 on Top Layer | Pad 1 [VBUS] of L1 on Top Layer
open: Pad 1 [VBUS] of C21 on Top Layer | Pad 1 [VBUS] of C20 on 6 Bottom Layer
open: Pad 1 [VBUS] of C21 on Top Layer | Pad 2 [VBUS] of R16 on Top Layer
open: Pad 2 [VBUS] of R12 on 6 Bottom Layer | Pad 1 [VBUS] of D2 on 6 Bottom Layer
open: Pad 1 [VBUS] of C17 on 6 Bottom Layer | Pad 1 [VBUS] of L1 on Top Layer
open: Pad 1 [VBUS] of C17 on 6 Bottom Layer | Pad 1 [VBUS] of D2 on 6 Bottom Layer
open: Pad 2 [VBUS] of U4 on 6 Bottom Layer | Pad 1 [VBUS] of R8 on 6 Bottom Layer
open: Pad 1 [VBUS] of R8 on 6 Bottom Layer | Pad 1 [VBUS] of TP22 on 6 Bottom Layer
open: Pad 2 [VBUS] of D1 on Top Layer | Pad 1 [VBUS] of R11 on 6 Bottom Layer
open: Pad 2 [VBUS] of D1 on Top Layer | Pad 1 [VBUS] of L1 on Top Layer
open: Pad 2 [VBUS] of D1 on Top Layer | Pad 1 [VBUS] of U11 on Top Layer
open: Pad 1 [VBUS] of TP22 on 6 Bottom Layer | Pad 1 [VBUS] of C55 on Top Layer
open: Pad 1 [VBUS] of C30 on Top Layer | Pad 2 [VBUS] of R39 on 6 Bottom Layer
open: Pad 1 [VBUS] of C54 on 6 Bottom Layer | Pad 1 [VBUS] of C55 on Top Layer
open: Pad 1 [VBUS] of C54 on 6 Bottom Layer | Pad 3 [VBUS] of U10 on Top Layer
open: Pad 1 [VBUS] of C29 on 6 Bottom Layer | Pad 1 [VBUS] of C30 on Top Layer
open: Pad 3 [VBUS] of U10 on Top Layer | Pad 2 [VBUS] of R39 on 6 Bottom Layer
open: Pad 3 [VBUS] of U5 on Top Layer | Pad 1 [VBUS] of C29 on 6 Bottom Layer
open: Pad 2 [VBUS] of R20 on 6 Bottom Layer | Pad 3 [VBUS] of U5 on Top Layer
open: Pad 1 [VBUS] of R41 on 6 Bottom Layer | Pad 1 [VBUS] of U11 on Top Layer
open: Pad 1 [VBUS] of R41 on 6 Bottom Layer | Pad 1 [VBUS] of C49 on Top Layer
open: Pad 2 [VBUS] of R15 on 6 Bottom Layer | Pad 1 [VBUS] of R41 on 6 Bottom Layer
open: Pad 2 [VBUS] of R15 on 6 Bottom Layer | Pad 2 [VBUS] of R20 on 6 Bottom Layer
open: Pad 1 [VBUS_OUT] of J5 on Top Layer | Pad 1 [VBUS_OUT] of TP36 on 6 Bottom Layer
open: Pad 2 [VBUS_OUT] of R11 on 6 Bottom Layer | Pad 1 [VBUS_OUT] of TP36 on 6 Bottom Layer
open: Pad 2 [VBUS_OUT] of R11 on 6 Bottom Layer | Pad 1 [VBUS_OUT] of D3 on 6 Bottom Layer
open: Pad 1 [VBUS_OUT] of D3 on 6 Bottom Layer | Pad 10 [VBUS_OUT] of U11 on Top Layer
open: Pad 1 [VBUS_OUT] of C50 on 6 Bottom Layer | Pad 10 [VBUS_OUT] of U11 on Top Layer
open: PTH pad 1 [unconnected-(J1-3V3-Pad1)] of J1 | PTH pad 17 [unconnected-(J1-3V3-Pad1)] of J1
