nickraymond/nereus_Pi_shield_ADIN2111/experiments/fable_layout_01a/out/m4/drc_summary.txt

7 ('clearance', 'error')
10 ('courtyards_overlap', 'error')
36 ('hole_clearance', 'error')
28 ('lib_footprint_mismatch', 'warning')
38 ('padstack', 'warning')
4 ('padstack_invalid', 'error')
34 ('shorting_items', 'error')
2 ('silk_overlap', 'warning')
18 ('solder_mask_bridge', 'error')
unconnected_items: 1
schematic_parity: 4
errors: 109  warnings: 68
open: PTH pad 1 [unconnected-(J1-3V3-Pad1)] of J1 | PTH pad 17 [unconnected-(J1-3V3-Pad1)] of J1
