nickraymond/nereus_Pi_shield_ADIN2111/experiments/fable_layout_01a/out/m5/drc_exclusions.md

# DRC exclusions (M5)

Generated by `tools/drcexclude.py` from the table of reasons in that script.

| Type | # | Reason |
|---|---|---|
| clearance | 1 | Sofar's P1L geometry copied as drawn: the 2.0 mm BM1_N stub at L1 pad 2 and Sofar's GND pour-stitching via 0.25 mm apart (DRC's figure; the mote's 0.2 mm rule, our bus rule asks 0.35). Experiment 01 trimmed the via as dangling; here the bottom GND pour keeps it |
| clearance | 2 | Sofar's transformer footprint: the copied vias of pads 3/4's nets sit beside the unnumbered no-net pads, as on the mote |
| clearance | 4 | Sofar's transformer footprint: two unnumbered no-net pads overlap pads 3/4 (identical on the mote board) |
| courtyards_overlap | 10 | Sofar's placement inside a copied block (rigid, BRIEF rule 5); the courtyards were added in S6.c and overlap where Sofar packed parts tighter |
| hole_clearance | 36 | Sofar's insert contact copied as drawn: the ring pad vs the 7 via holes (28), the NPTH vs the ring pad (4) and the arc/vias vs the 4.4 mm hole (4), as on the mote (Sofar Q6) |
| padstack_invalid | 4 | Sofar's insert footprint (Altium import): the NPTH pad has no copper size; hole 4.4 mm (DESIGN D19/D24) |
| shorting_items | 28 | Sofar's insert contact copied as drawn (BRIEF §3): bus vias land in the insert's net-less ring pad (Sofar Q6) |
| shorting_items | 6 | Sofar's transformer footprint: tracks to pads 3/4 cross the unnumbered no-net pads, as on the mote |
| solder_mask_bridge | 8 | Sofar's insert contact copied as drawn: the ring pad's mask opening spans the bus vias (Sofar Q6) |
| solder_mask_bridge | 10 | Sofar's transformer footprint: the unnumbered no-net pads' mask openings touch pads 3/4, as on the mote |

kicad-cli DRC: 109 errors, 109 with a reason above, 0 without; 1 unconnected, 4 parity items (the 4 parity items are MP1–4 pin 1, Sofar Q6).
