nickraymond/nereus_Pi_shield_ADIN2111/experiments/fable_layout_01a/review_head.html

# Layout experiment 1.a: design review (session 2.b)

Board 49 × 68 mm (session 2.b, Nick's 3 + 3 mm), the fitted 20 W inductors' courtyards + 2 mm as the keep-out, U1 in the west pocket 8.8 mm from the edge (the centre placement did not route: OPTIONS.md addendum A3), the SPI on a reserved Internal 2 lane routed first, the inserts 1.5 mm nearer the wall, the jumpers on top at the north edge, JLCPCB's limits in the design rules (DFM.md), no router via in any solder pad. Left: Sofar's mote, its copper placed as this board places the block. Right: this board. Generated by tools/review_views.py; the numbers are in out/m4/summary.json. The before / after page shows session 2's board beside this one, layer by layer.
