nickraymond/nereus_Pi_shield_ADIN2111/experiments/fable_layout_01a/out/review/index.html

# Layout experiment 1.a: design review (session 2.b)

Board 49 × 68 mm (session 2.b, Nick's 3 + 3 mm), the fitted 20 W inductors' courtyards + 2 mm as the keep-out, U1 in the west pocket 8.8 mm from the edge (the centre placement did not route: OPTIONS.md addendum A3), the SPI on a reserved Internal 2 lane routed first, the inserts 1.5 mm nearer the wall, the jumpers on top at the north edge, JLCPCB's limits in the design rules (DFM.md), no router via in any solder pad. Left: Sofar's mote, its copper placed as this board places the block. Right: this board. Generated by tools/review_views.py; the numbers are in out/m4/summary.json. The before / after page shows session 2's board beside this one, layer by layer.

Colours: data pairs bus VBUS 3V3 rails 5 V to the Pi signals / GND tracks GND fills. Left: Sofar's mote, its copper placed as this board places the block. Right: this board. Same renderer, same region, same scale (grid 0.1 mm cells; the images are 40 px/mm).

## port1 pair x -3.5…10.5, y 25.5…32.5 mm · block ADIN

Port-1 data pair: U1 pins 27/28 (north edge of U1 at rot 90) to T1 pads 1/2 in the band; the mote's U1 and T1 sit elsewhere, so the mote view shows only the ADIN block's copper placed as here

Fixed / as built: Session 2.b: the pair's 45° runs are single segments (15 segments per leg, was 25) and the P leg keeps 0.11 mm under the mote's 9.5 (9.39 / 8.77; T1 0.2 mm north of session 2's relation). Two vias straight out of U1's pins, Internal 1, one swap, Top into T1's pads along the straight lane.

Versus the mote: Sofar leaves the pins by vias 0.75 / 1.1 mm out and runs the port on Internal 1 too, but enters T1's pads from the body side with a via behind each pad; here the pads face U1 and the pair enters from the open side.

Still open: 0.11 mm of margin on P: a rerun is not byte-identical. The centre placement (OPTIONS addendum A3) would give the mote's own geometry but needs the body-side entry to route.

mote port1_pair Top

Sofar's mote, Top (block ADIN transform)

board port1_pair Top

This board, Top

mote port1_pair Internal 1

Sofar's mote, Internal 1 (block ADIN transform)

board port1_pair Internal 1

This board, Internal 1

mote port1_pair Bottom

Sofar's mote, Bottom (block ADIN transform)

board port1_pair Bottom

This board, Bottom

## port2 pair x -4.0…14.0, y 34.0…41.5 mm · block ADIN

Port-2 data pair: U1 pins 4/5 (south edge) through the pocket's south exit to T2 pads 1/2

Fixed / as built: Leaves U1 pins 4/5 on Top through the pocket's south exit (3 mm taller than session 2), swaps once, gets its via pair beside T2's approach. 19.93 / 20.61 mm (mote 21.3; session 2 17.98 / 18.62: the exit is 1.25 mm further south now).

Versus the mote: Sofar's port 2 is 21 mm of Internal 1 to a T2 on the far side of the processor.

Still open: None at the bar; the margin is 0.7 mm.

mote port2_pair Top

Sofar's mote, Top (block ADIN transform)

board port2_pair Top

This board, Top

mote port2_pair Internal 1

Sofar's mote, Internal 1 (block ADIN transform)

board port2_pair Internal 1

This board, Internal 1

mote port2_pair Bottom

Sofar's mote, Bottom (block ADIN transform)

board port2_pair Bottom

This board, Bottom
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
