nickraymond/nereus_Pi_shield_ADIN2111/experiments/fable_layout_01/out/m1/render_top.png

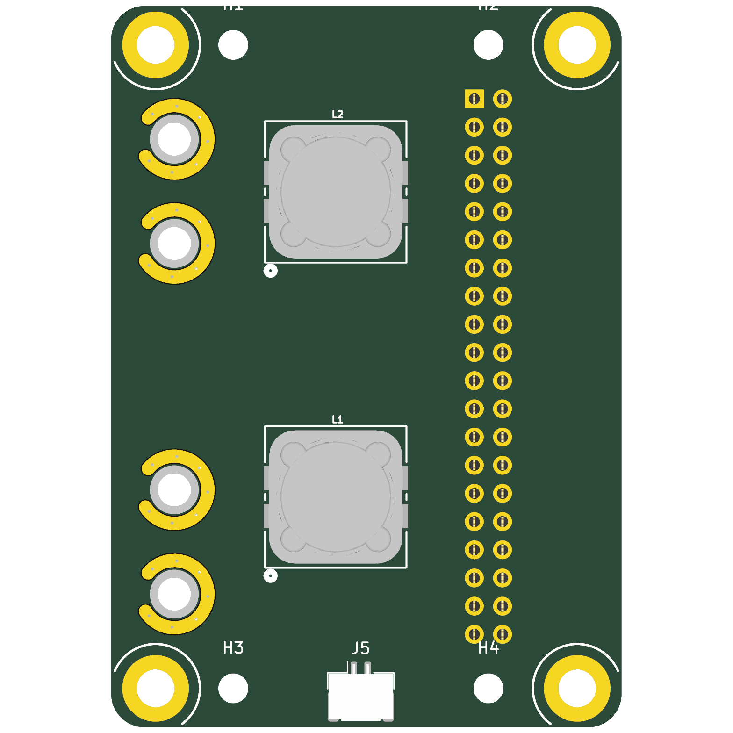
experiments/fable_layout_01/out/m1/render_top.png
