nickraymond/nereus_Pi_shield_ADIN2111/experiments/fable_layout_01a/out/m4/render_top.png

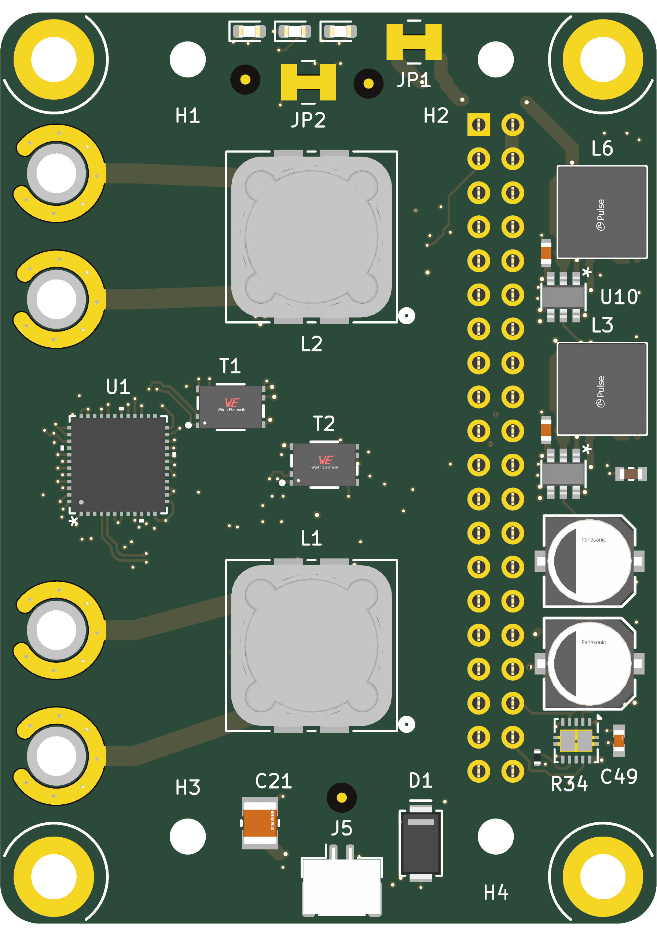
experiments/fable_layout_01a/out/m4/render_top.png
